npgo22/APRL-Electrical/kicadlibs/models/Texas_HTSSOP-14-1EP_4.4x5mm_P0.65mm_EP3.4x5mm_Mask3.155x3.255mm.step

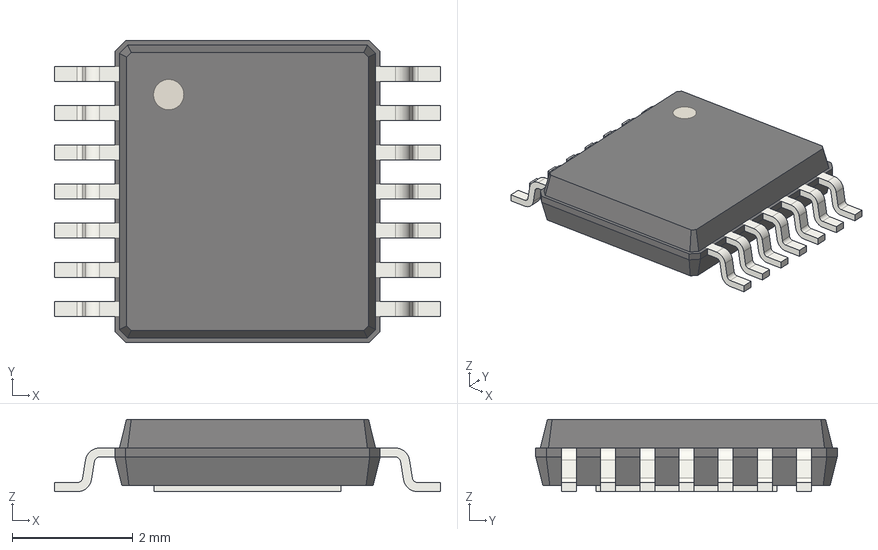
[picture p17: CAD file, 2026-09-21]
kicadlibs/models/Texas_HTSSOP-14-1EP_4.4x5mm_P0.65mm_EP3.4x5mm_Mask3.155x3.255mm.step
6.40 x 5.00 x 1.20 mm
