npgo22/APRL-Electrical/kicadlibs/models/WSON-6-1EP_2x2mm_P0.65mm_EP1x1.6mm.step

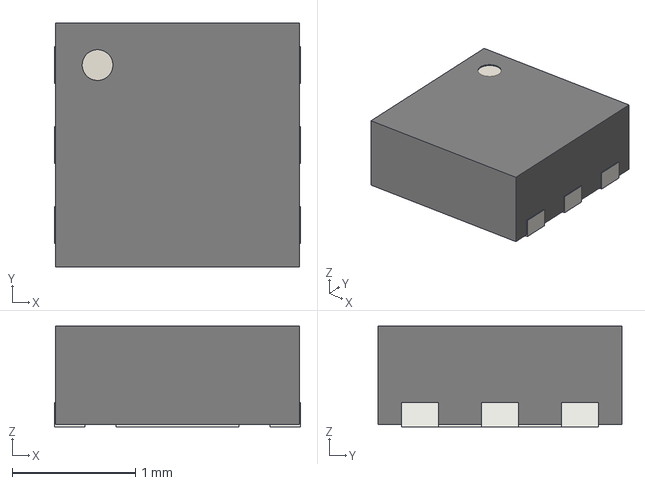
[picture p18: CAD file, 2026-09-21]
kicadlibs/models/WSON-6-1EP_2x2mm_P0.65mm_EP1x1.6mm.step
2.00 x 1.98 x 0.82 mm
