npgo22/APRL-Electrical/kicadlibs/models/Molex_CLIK-Mate_503175-0500_1x05-1MP_P1.50mm_Horizontal.step

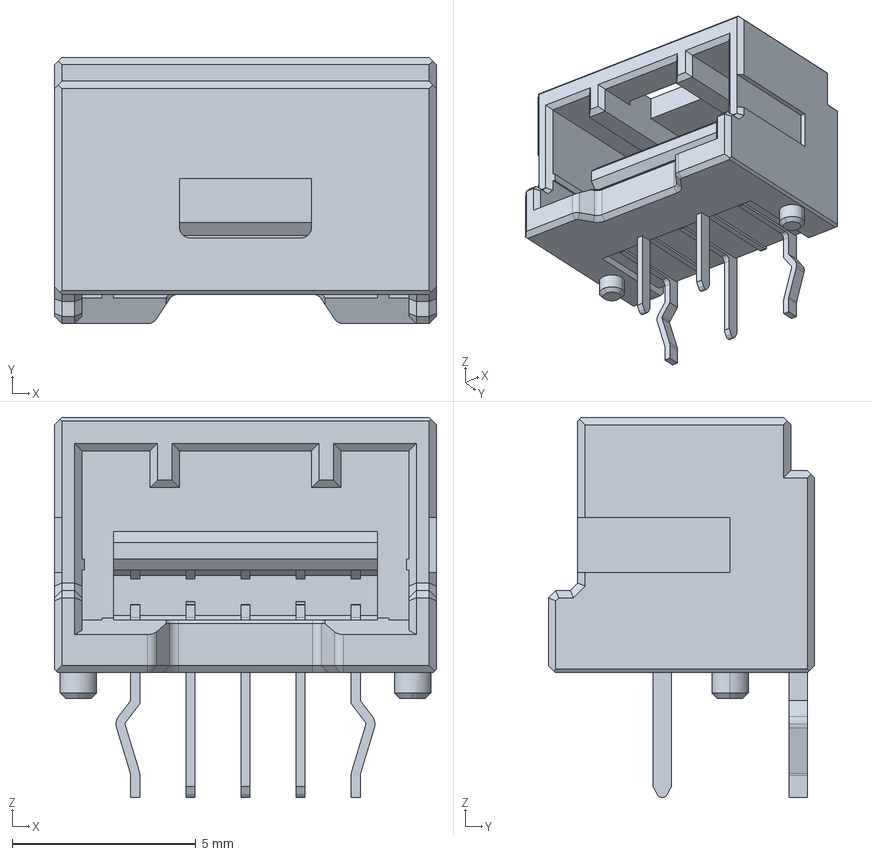
[picture p19: CAD file, 2026-09-17]
kicadlibs/models/Molex_CLIK-Mate_503175-0500_1x05-1MP_P1.50mm_Horizontal.step
10.4 x 7.25 x 10.4 mm
