npgo22/APRL-Electrical/kicadlibs/models/GPSM-SMD_NEO-M8N.step

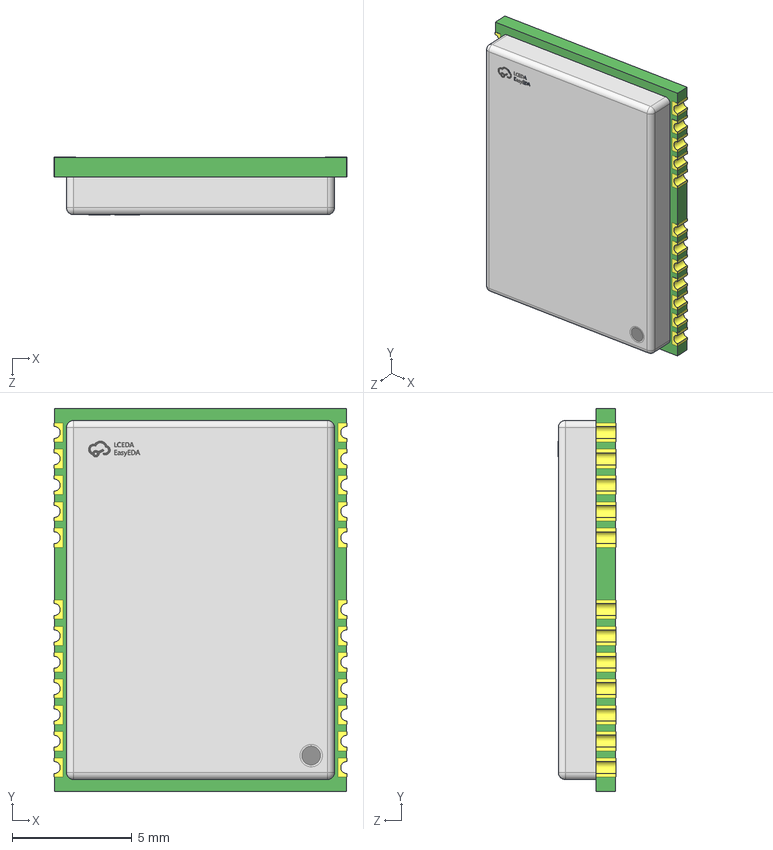
[picture p20: CAD file, 2026-09-17]
kicadlibs/models/GPSM-SMD_NEO-M8N.step
12.2 x 16.0 x 2.42 mm
