npgo22/APRL-Electrical/kicadlibs/models/Molex_CLIK-Mate_503159-1401_1x14-1MP_P1.50mm_Vertical.step

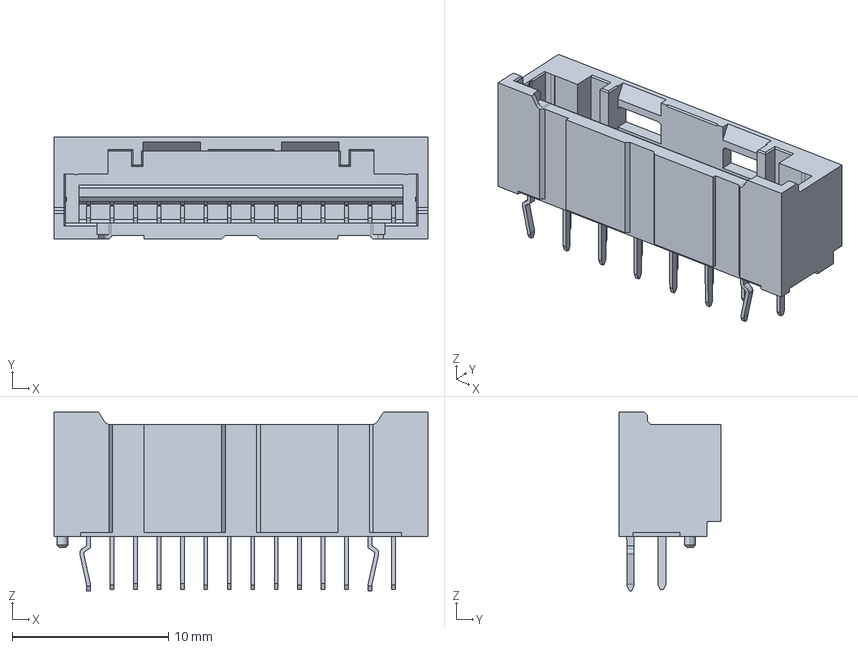
[picture p22: CAD file, 2026-09-17]
kicadlibs/models/Molex_CLIK-Mate_503159-1401_1x14-1MP_P1.50mm_Vertical.step
23.9 x 6.55 x 11.4 mm
