npgo22/APRL-Electrical/kicadlibs/models/QFN-32-1EP_5x5mm_P0.5mm_EP3.3x3.3mm.step

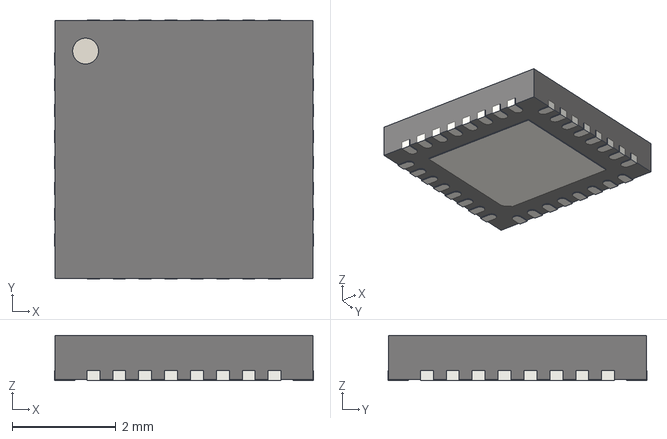
[picture p23: CAD file, 2026-09-17]
kicadlibs/models/QFN-32-1EP_5x5mm_P0.5mm_EP3.3x3.3mm.step
5.00 x 5.00 x 0.875 mm
