npgo22/APRL-Electrical/kicadlibs/models/D_SMF.step

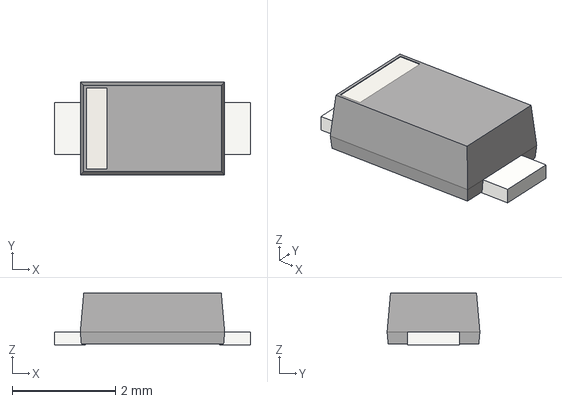
[picture p24: CAD file, 2026-09-17]
kicadlibs/models/D_SMF.step
3.80 x 1.80 x 1.00 mm
