npgo22/APRL-Electrical/kicadlibs/models/Molex_CLIK-Mate_503175-1400_1x14-1MP_P1.50mm_Horizontal.step

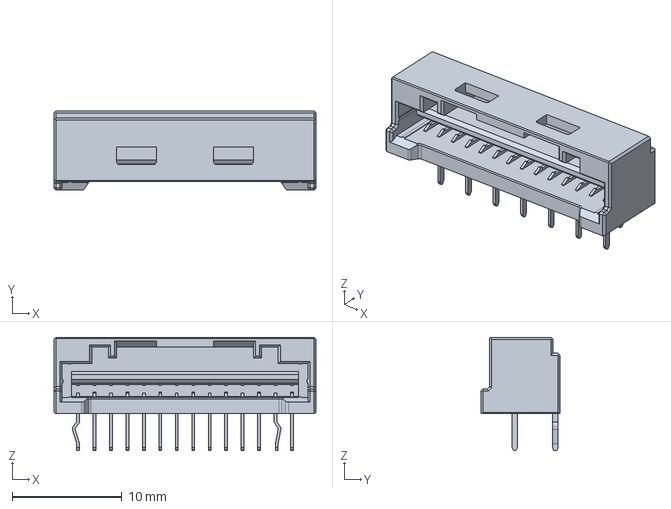
[picture p25: CAD file, 2026-09-17]
kicadlibs/models/Molex_CLIK-Mate_503175-1400_1x14-1MP_P1.50mm_Horizontal.step
23.9 x 7.25 x 10.4 mm
