npgo22/APRL-Electrical/kicadlibs/models/CRYSTAL-SMD_4P-L3.2-W2.5-BL-2.step

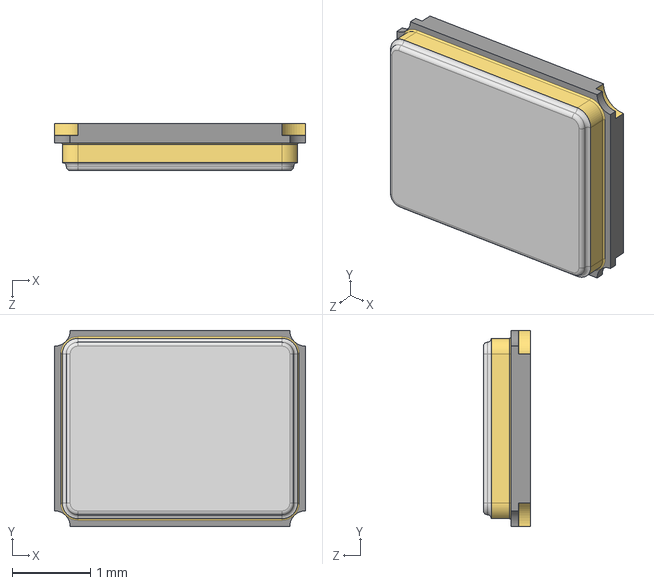
[picture p26: CAD file, 2026-09-17]
kicadlibs/models/CRYSTAL-SMD_4P-L3.2-W2.5-BL-2.step
3.20 x 2.50 x 0.601 mm
