npgo22/APRL-Electrical/kicadlibs/models/Molex_CLIK-Mate_503175-0200_1x02-1MP_P1.50mm_Horizontal.step

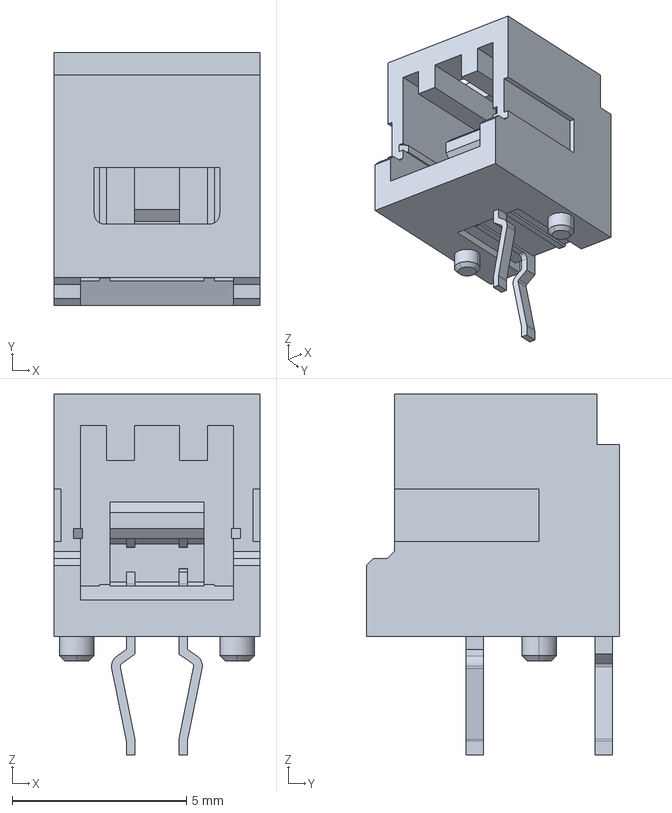
[picture p27: CAD file, 2026-09-17]
kicadlibs/models/Molex_CLIK-Mate_503175-0200_1x02-1MP_P1.50mm_Horizontal.step
5.90 x 7.25 x 10.4 mm
