npgo22/APRL-Electrical/kicadlibs/models/LQFP-48_7x7mm_P0.5mm.step

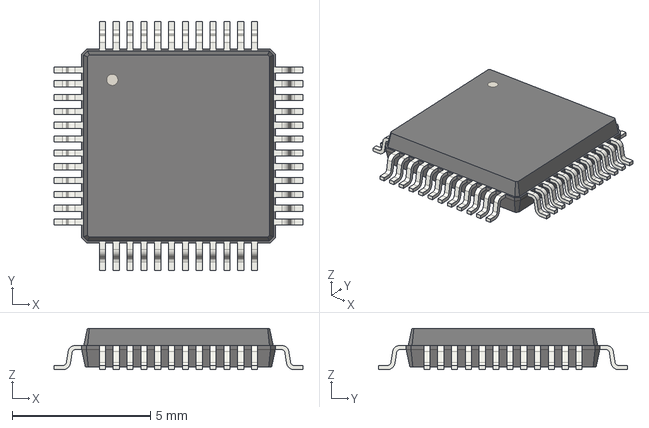
[picture p29: CAD file, 2026-09-17]
kicadlibs/models/LQFP-48_7x7mm_P0.5mm.step
9.00 x 9.00 x 1.50 mm
