npgo22/APRL-Electrical/kicadlibs/models/Molex_CLIK-Mate_503175-1300_1x13-1MP_P1.50mm_Horizontal.step

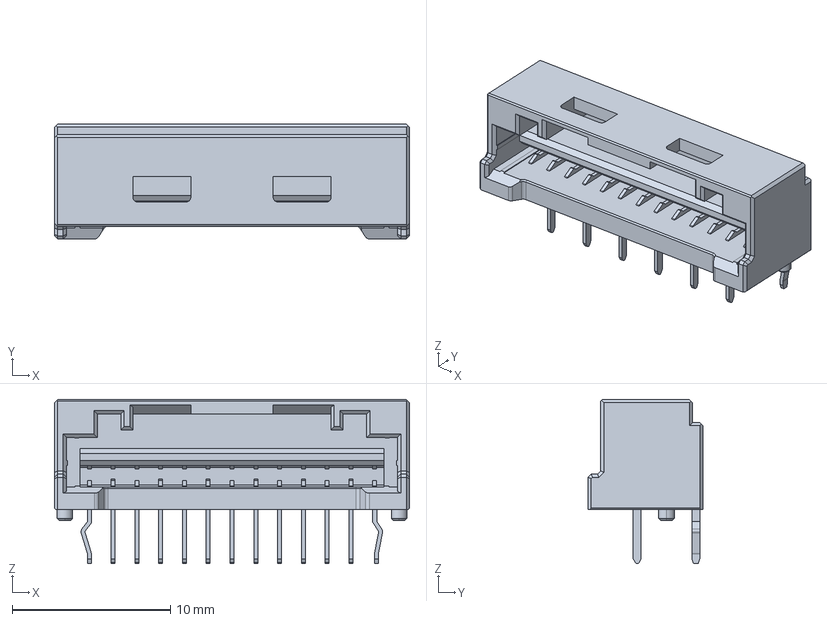
[picture p30: CAD file, 2026-09-17]
kicadlibs/models/Molex_CLIK-Mate_503175-1300_1x13-1MP_P1.50mm_Horizontal.step
22.4 x 7.25 x 10.4 mm
