npgo22/APRL-Electrical/kicadlibs/models/Molex_CLIK-Mate_503175-0300_1x03-1MP_P1.50mm_Horizontal.step

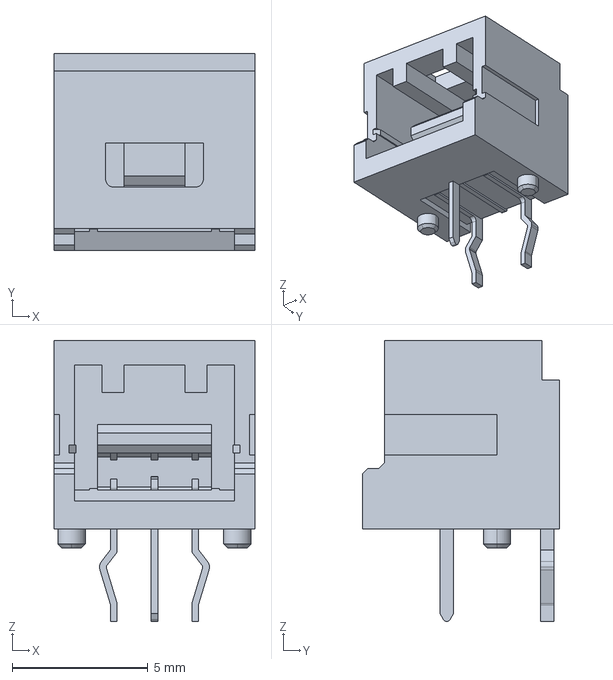
[picture p31: CAD file, 2026-09-17]
kicadlibs/models/Molex_CLIK-Mate_503175-0300_1x03-1MP_P1.50mm_Horizontal.step
7.40 x 7.25 x 10.4 mm
