npgo22/APRL-Electrical/kicadlibs/models/Molex_CLIK-Mate_503175-0800_1x08-1MP_P1.50mm_Horizontal.step

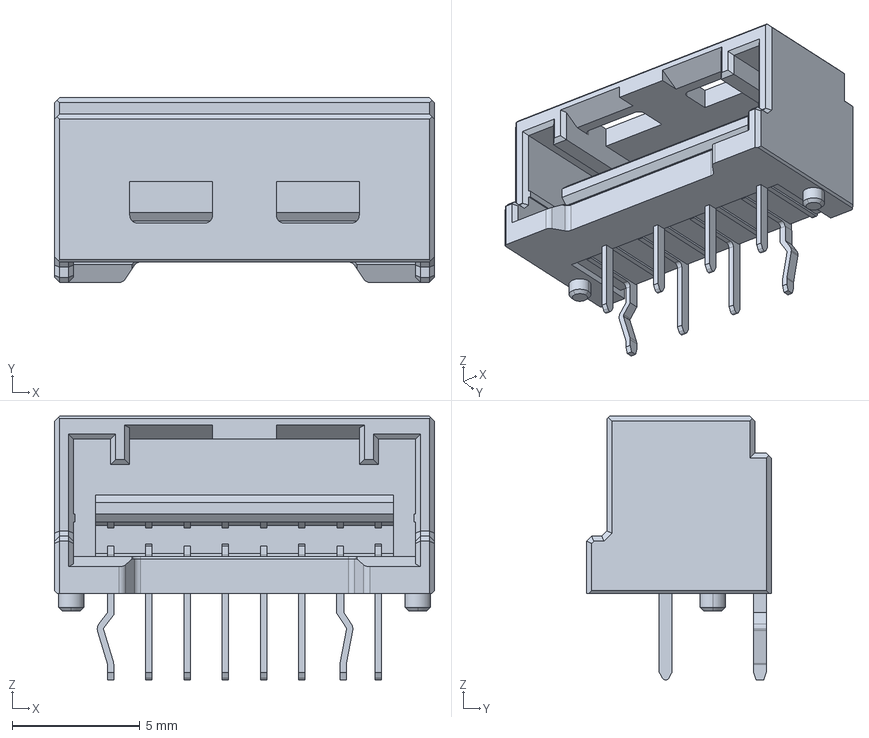
[picture p32: CAD file, 2026-09-17]
kicadlibs/models/Molex_CLIK-Mate_503175-0800_1x08-1MP_P1.50mm_Horizontal.step
14.9 x 7.25 x 10.4 mm
