npgo22/APRL-Electrical/kicadlibs/models/PhoenixContact_MSTB_2,5_2-GF-5,08_1x02_P5.08mm_Horizontal_ThreadedFlange_MountHole.step

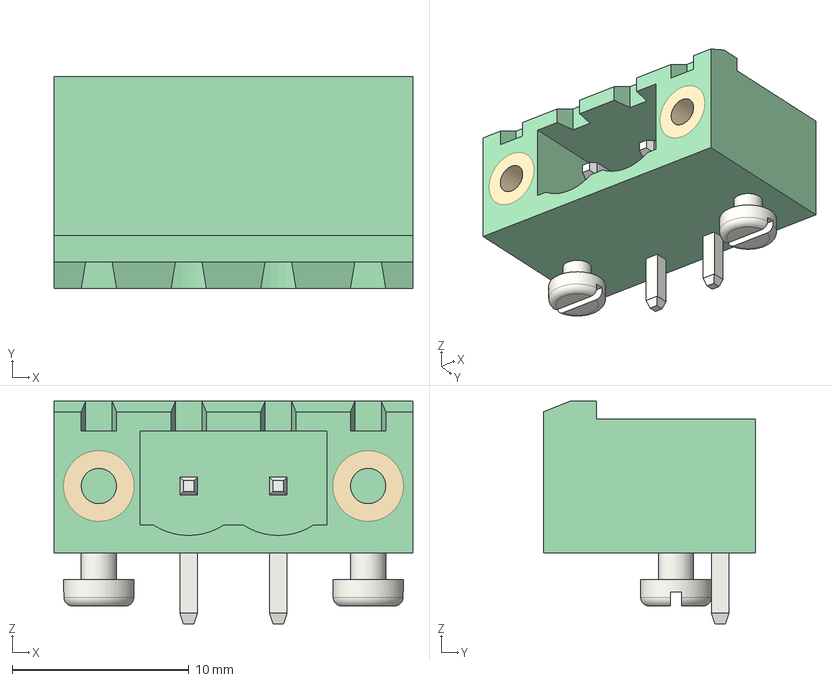
[picture p33: CAD file, 2026-09-17]
kicadlibs/models/PhoenixContact_MSTB_2,5_2-GF-5,08_1x02_P5.08mm_Horizontal_ThreadedFlange_MountHole.step
20.3 x 12.0 x 12.6 mm
