npgo22/APRL-Electrical/kicadlibs/models/R_0805_2012Metric.step

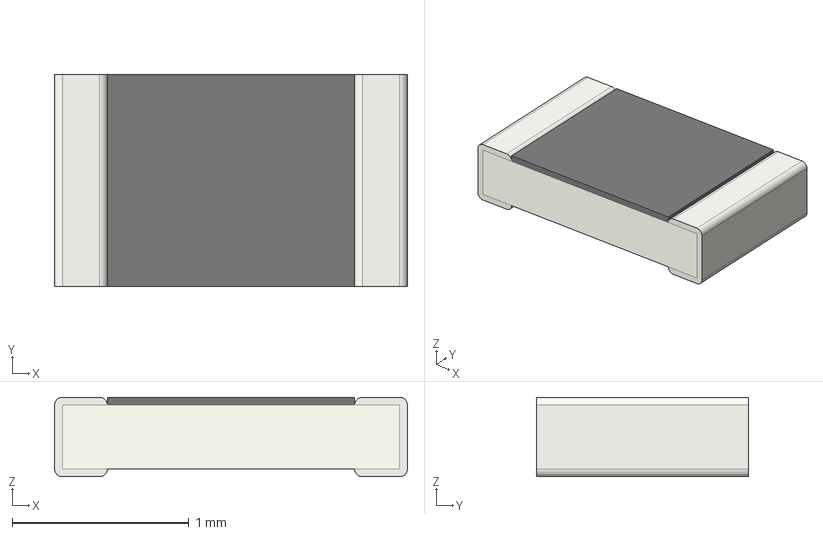
[picture p34: CAD file, 2026-09-17]
kicadlibs/models/R_0805_2012Metric.step
2.00 x 1.20 x 0.45 mm
