npgo22/APRL-Electrical/kicadlibs/models/TerminalBlock_Phoenix_MKDS-1,5-2-5.08_1x02_P5.08mm_Horizontal.step

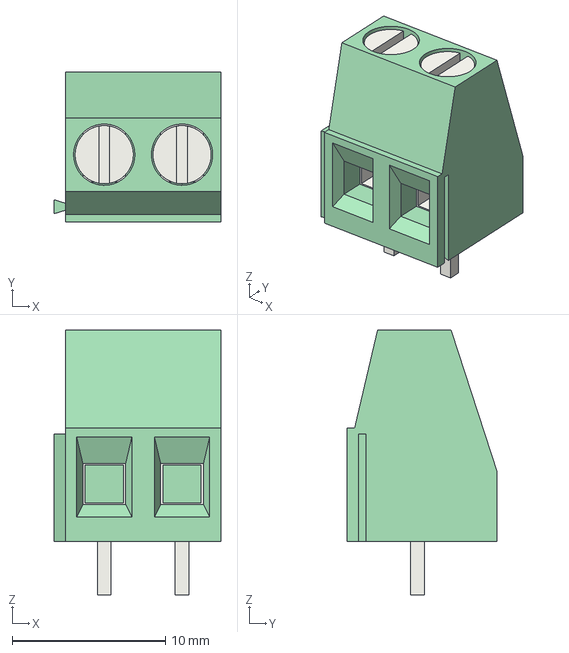
[picture p36: CAD file, 2026-09-17]
kicadlibs/models/TerminalBlock_Phoenix_MKDS-1,5-2-5.08_1x02_P5.08mm_Horizontal.step
10.9 x 9.80 x 17.3 mm
