npgo22/APRL-Electrical/kicadlibs/models/Molex_CLIK-Mate_503175-1100_1x11-1MP_P1.50mm_Horizontal.step

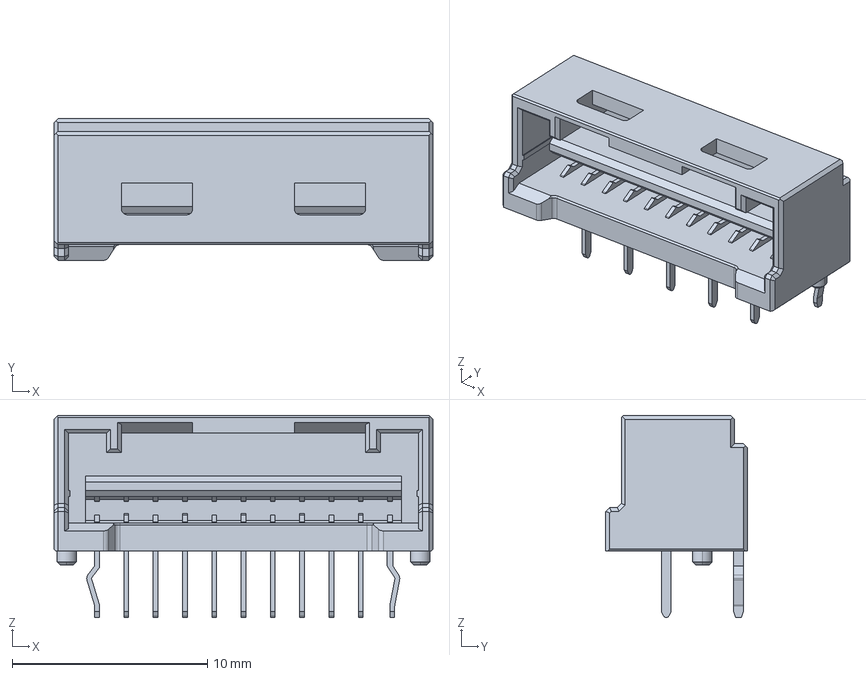
[picture p37: CAD file, 2026-09-17]
kicadlibs/models/Molex_CLIK-Mate_503175-1100_1x11-1MP_P1.50mm_Horizontal.step
19.4 x 7.25 x 10.4 mm
