npgo22/APRL-Electrical/kicadlibs/models/IDC-Header_2x09_P2.54mm_Vertical.step

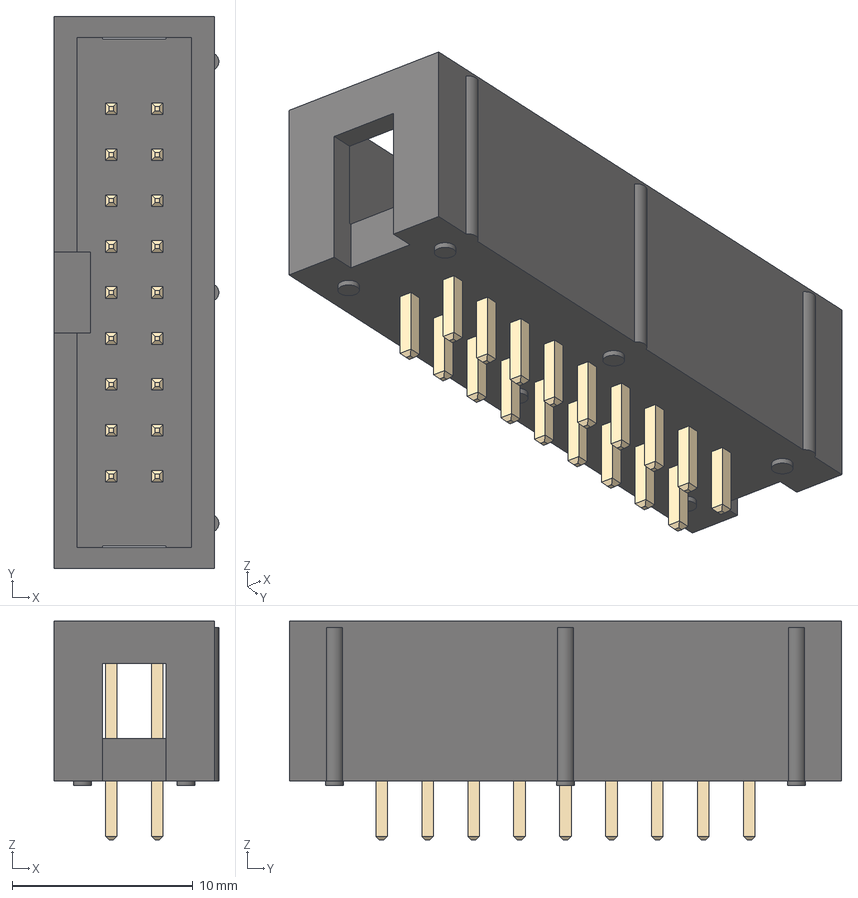
[picture p38: CAD file, 2026-09-17]
kicadlibs/models/IDC-Header_2x09_P2.54mm_Vertical.step
9.10 x 30.5 x 12.1 mm
