npgo22/APRL-Electrical/kicadlibs/models/RJ45-TH_HR911105A.step

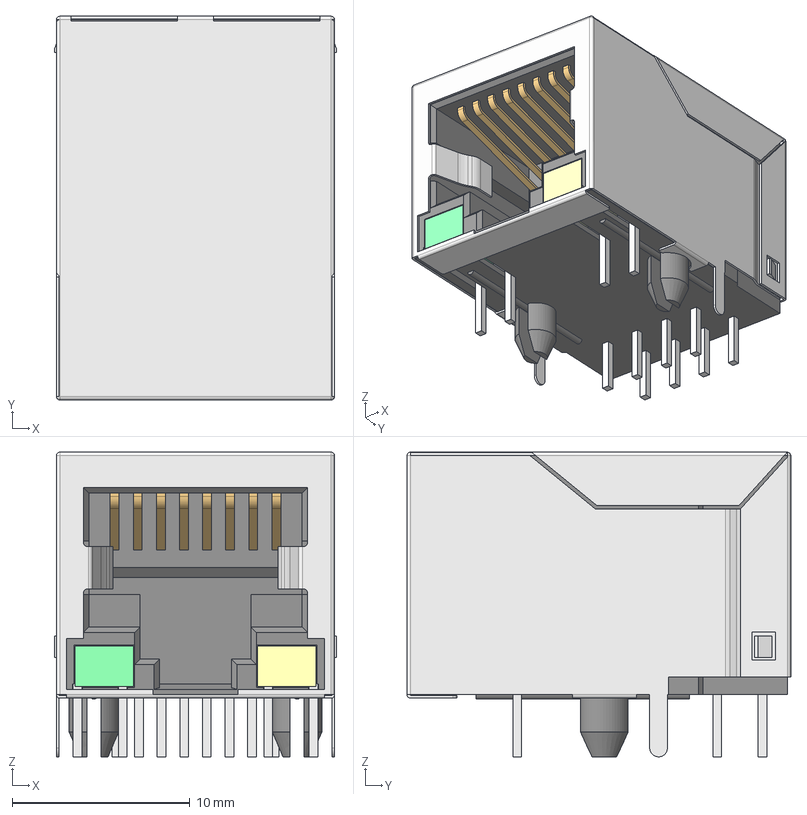
[picture p39: CAD file, 2026-09-17]
kicadlibs/models/RJ45-TH_HR911105A.step
15.9 x 21.6 x 17.1 mm
