npgo22/APRL-Electrical/kicadlibs/models/SOP-12_L5.6-W4.4-P0.80-LS7.0-BL.step

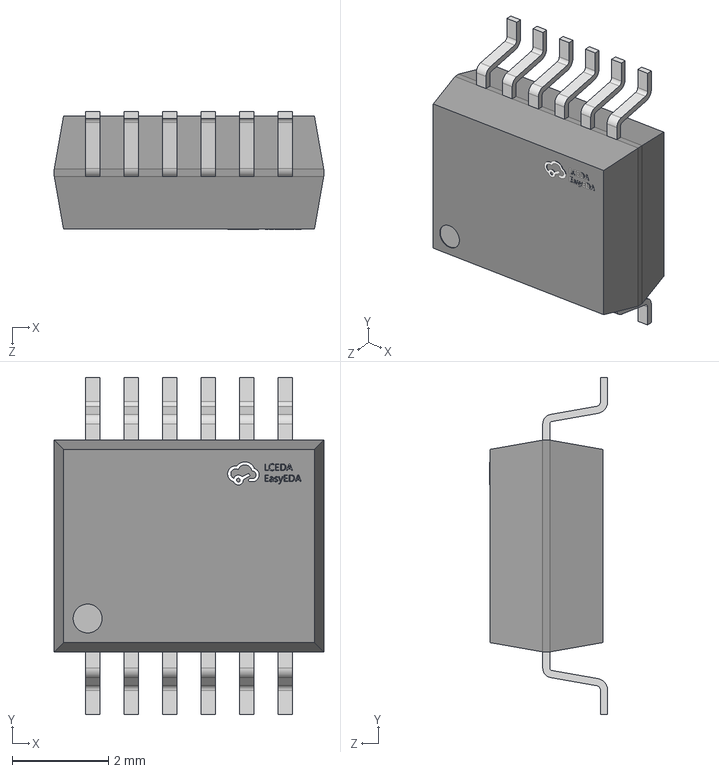
[picture p40: CAD file, 2026-09-17]
kicadlibs/models/SOP-12_L5.6-W4.4-P0.80-LS7.0-BL.step
5.60 x 7.00 x 2.46 mm
