npgo22/APRL-Electrical/kicadlibs/models/Fuse_0805_2012Metric.step

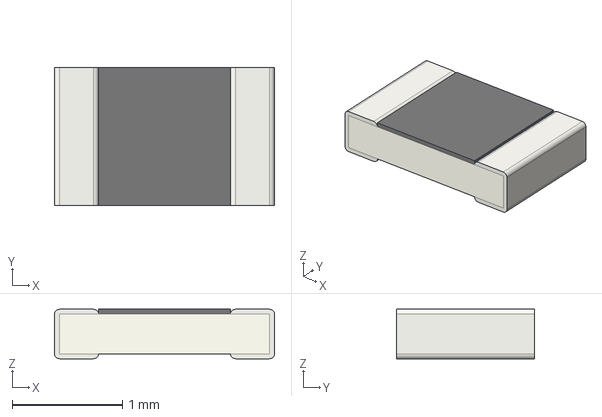
[picture p41: CAD file, 2026-09-17]
kicadlibs/models/Fuse_0805_2012Metric.step
2.00 x 1.25 x 0.45 mm
