npgo22/APRL-Electrical/kicadlibs/models/WSON-6_1.5x1.5mm_P0.5mm.step

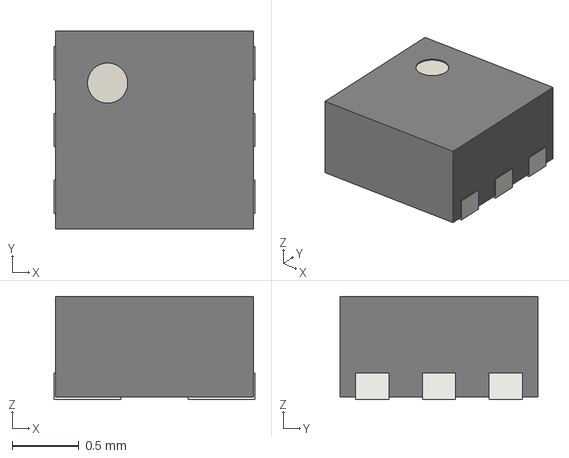
[picture p42: CAD file, 2026-09-17]
kicadlibs/models/WSON-6_1.5x1.5mm_P0.5mm.step
1.50 x 1.48 x 0.77 mm
