npgo22/APRL-Electrical/kicadlibs/models/DFN-8-1EP_3x3mm_P0.65mm_EP1.55x2.4mm.step

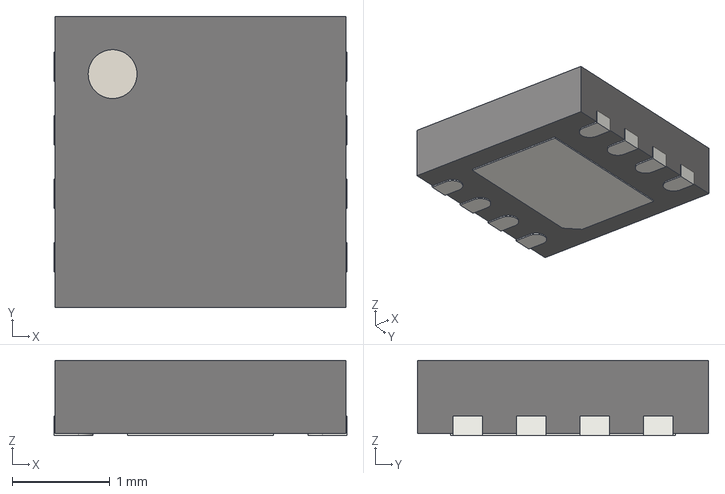
[picture p43: CAD file, 2026-09-17]
kicadlibs/models/DFN-8-1EP_3x3mm_P0.65mm_EP1.55x2.4mm.step
3.00 x 2.98 x 0.77 mm
