npgo22/APRL-Electrical/kicadlibs/models/Molex_CLIK-Mate_503159-1501_1x15-1MP_P1.50mm_Vertical.step

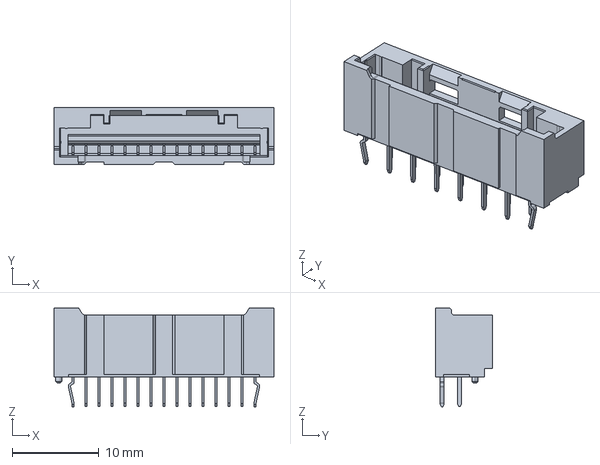
[picture p44: CAD file, 2026-09-17]
kicadlibs/models/Molex_CLIK-Mate_503159-1501_1x15-1MP_P1.50mm_Vertical.step
25.4 x 6.55 x 11.4 mm
