npgo22/APRL-Electrical/kicadlibs/models/QFN-32-1EP_5x5mm_P0.5mm_EP3.45x3.45mm.step

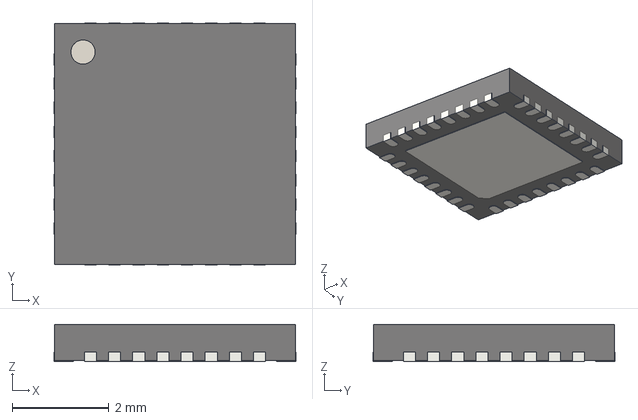
[picture p46: CAD file, 2026-09-17]
kicadlibs/models/QFN-32-1EP_5x5mm_P0.5mm_EP3.45x3.45mm.step
5.00 x 5.00 x 0.77 mm
