npgo22/APRL-Electrical/kicadlibs/models/s02-25200300.step

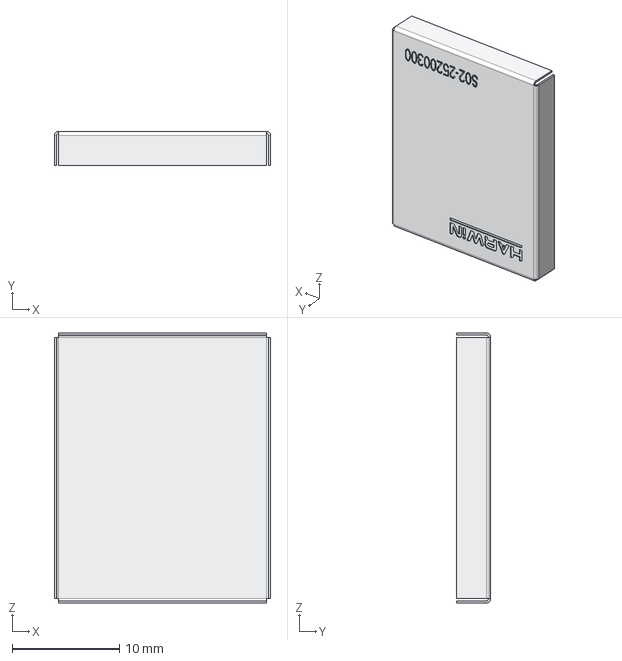
[picture p47: CAD file, 2026-09-17]
kicadlibs/models/s02-25200300.step
20.2 x 3.20 x 25.2 mm
