npgo22/APRL-Electrical/kicadlibs/models/DFN8_2x3MC_MCH.step

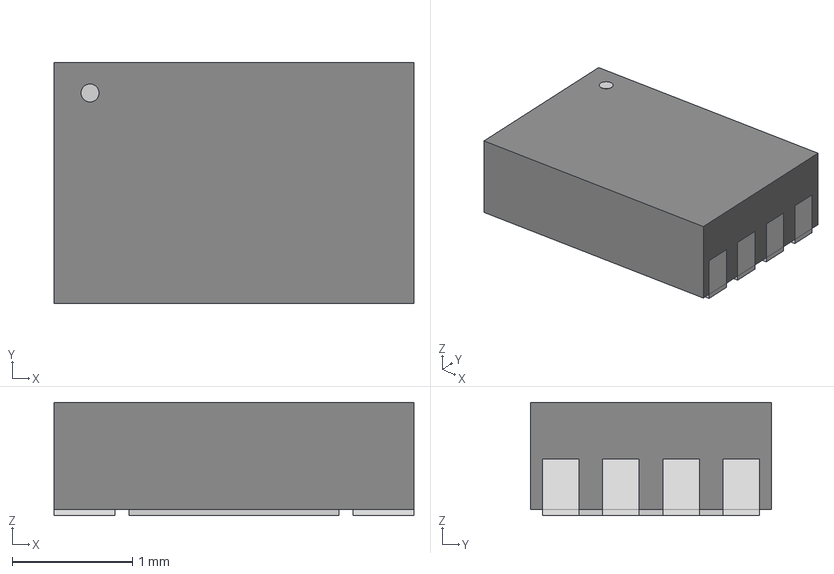
[picture p48: CAD file, 2026-09-17]
kicadlibs/models/DFN8_2x3MC_MCH.step
3.00 x 2.01 x 0.942 mm
