npgo22/APRL-Electrical/kicadlibs/models/TQFP-32.STEP

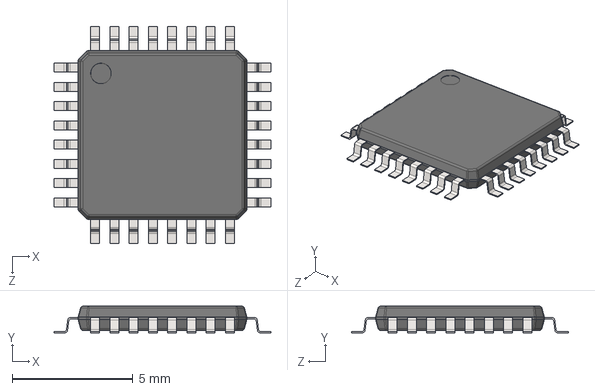
[picture p49: CAD file, 2026-09-17]
kicadlibs/models/TQFP-32.STEP
9.00 x 1.10 x 9.00 mm
