npgo22/APRL-Electrical/kicadlibs/models/PinHeader_1x05_P2.54mm_Vertical.step

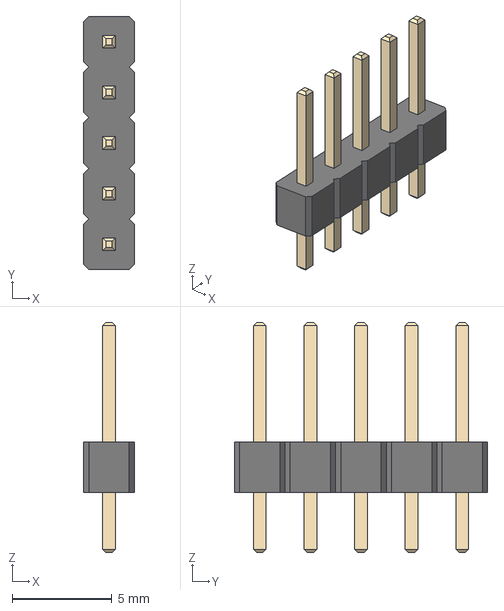
[picture p50: CAD file, 2026-09-17]
kicadlibs/models/PinHeader_1x05_P2.54mm_Vertical.step
2.54 x 12.7 x 11.5 mm
