npgo22/APRL-Electrical/kicadlibs/models/IDC-Header_2x06_P2.54mm_Vertical.step

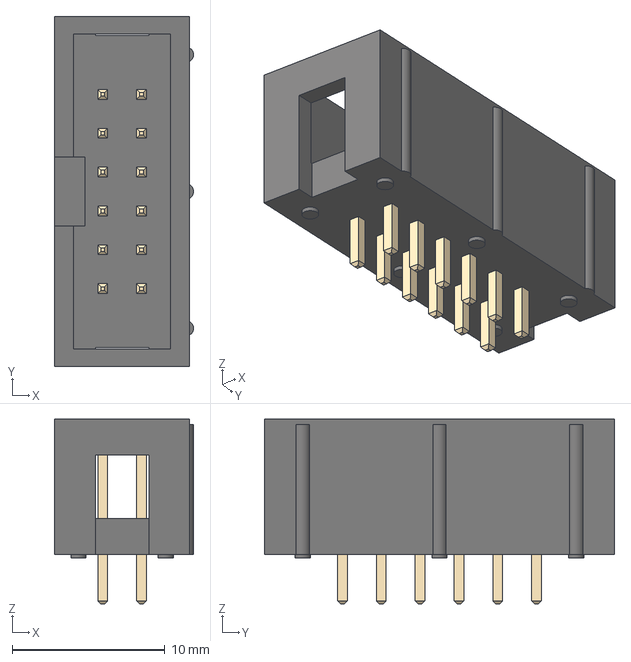
[picture p51: CAD file, 2026-09-17]
kicadlibs/models/IDC-Header_2x06_P2.54mm_Vertical.step
9.10 x 22.9 x 12.1 mm
