npgo22/APRL-Electrical/kicadlibs/models/Molex_CLIK-Mate_503175-1500_1x15-1MP_P1.50mm_Horizontal.step

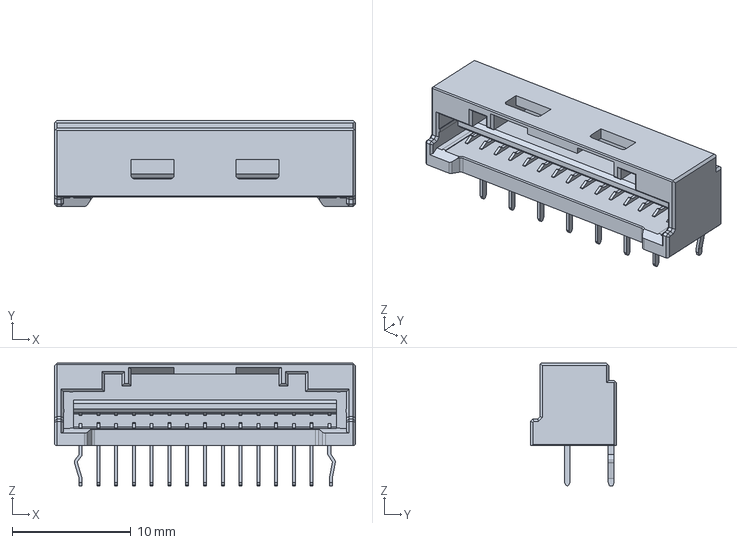
[picture p52: CAD file, 2026-09-17]
kicadlibs/models/Molex_CLIK-Mate_503175-1500_1x15-1MP_P1.50mm_Horizontal.step
25.4 x 7.25 x 10.4 mm
