npgo22/APRL-Electrical/kicadlibs/models/L_0402_1005Metric.step

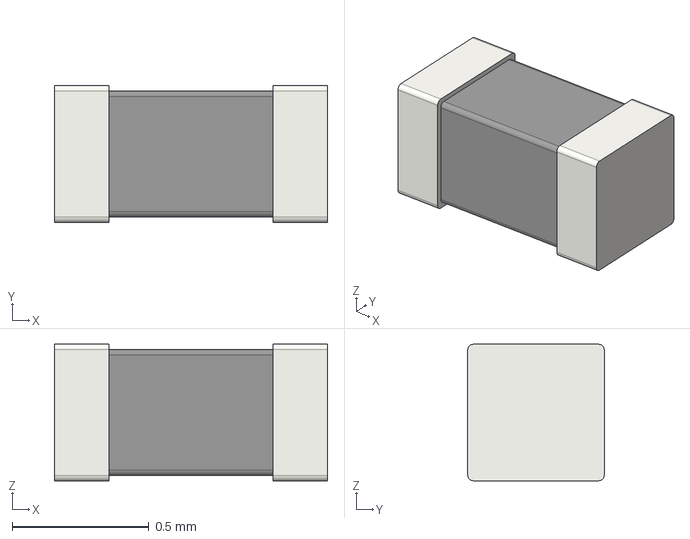
[picture p53: CAD file, 2026-09-17]
kicadlibs/models/L_0402_1005Metric.step
1.00 x 0.5 x 0.5 mm
