npgo22/APRL-Electrical/kicadlibs/models/PhoenixContact_MSTBV_2,5_2-GF-5,08_1x02_P5.08mm_Vertical_ThreadedFlange_MountHole.step

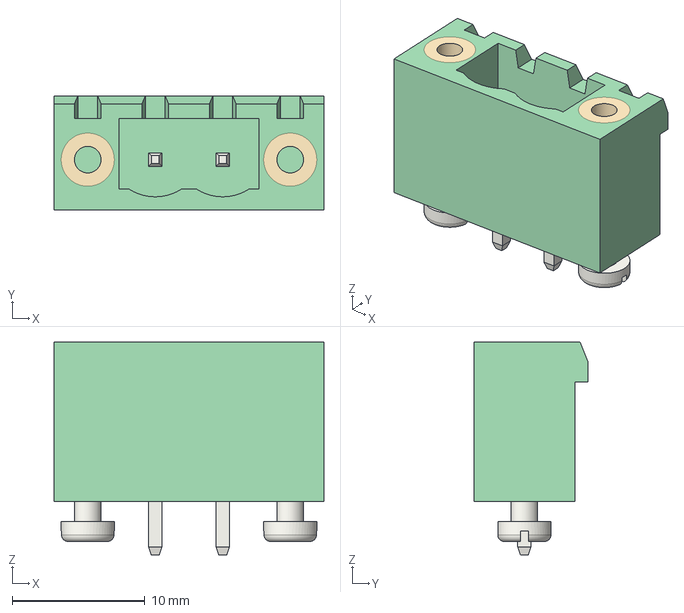
[picture p54: CAD file, 2026-09-17]
kicadlibs/models/PhoenixContact_MSTBV_2,5_2-GF-5,08_1x02_P5.08mm_Vertical_ThreadedFlange_MountHole.step
20.3 x 8.60 x 16.0 mm
