npgo22/APRL-Electrical/kicadlibs/models/SOT-23-5.step

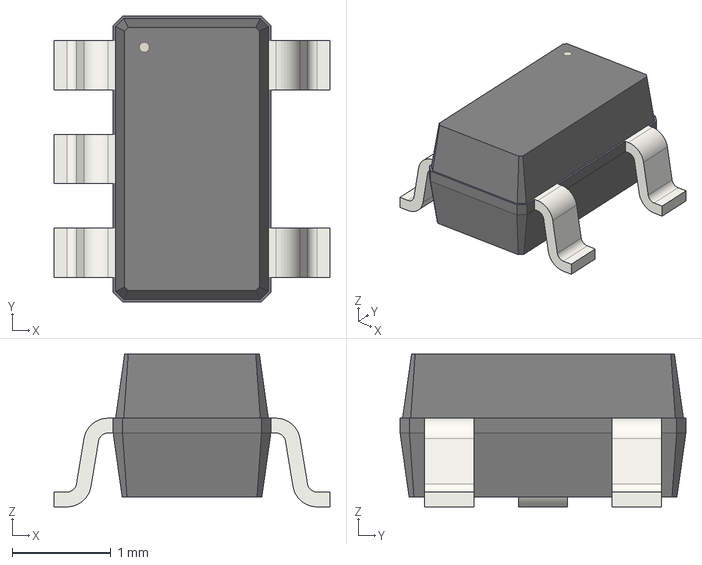
[picture p55: CAD file, 2026-09-17]
kicadlibs/models/SOT-23-5.step
2.80 x 2.90 x 1.55 mm
