npgo22/APRL-Electrical/kicadlibs/models/Molex_CLIK-Mate_503159-0401_1x04-1MP_P1.50mm_Vertical.step

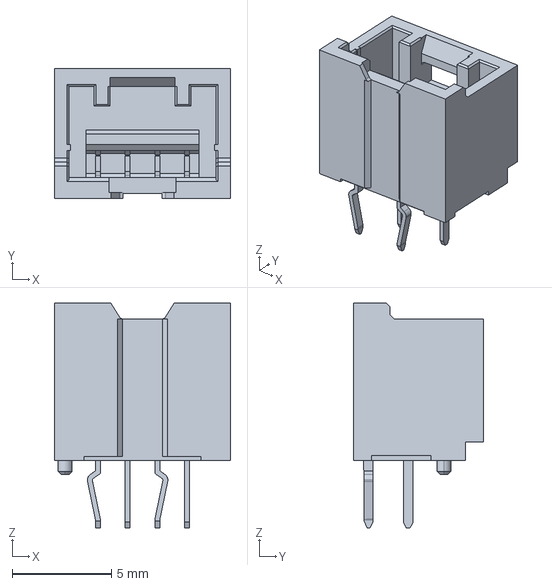
[picture p56: CAD file, 2026-09-17]
kicadlibs/models/Molex_CLIK-Mate_503159-0401_1x04-1MP_P1.50mm_Vertical.step
8.90 x 6.55 x 11.4 mm
