npgo22/APRL-Electrical/kicadlibs/models/LQFP-64_10x10mm_P0.5mm.step

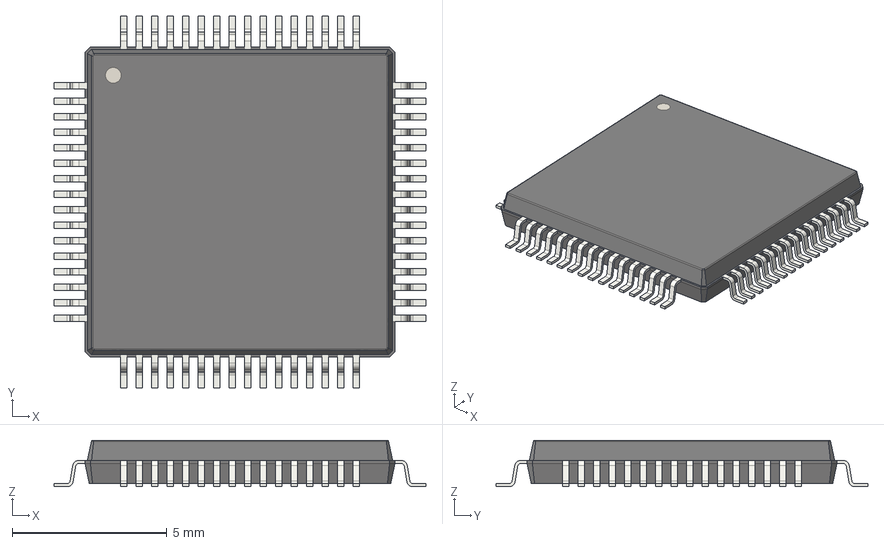
[picture p57: CAD file, 2026-09-17]
kicadlibs/models/LQFP-64_10x10mm_P0.5mm.step
12.0 x 12.0 x 1.50 mm
