npgo22/APRL-Electrical/kicadlibs/models/Molex_CLIK-Mate_503175-1200_1x12-1MP_P1.50mm_Horizontal.step

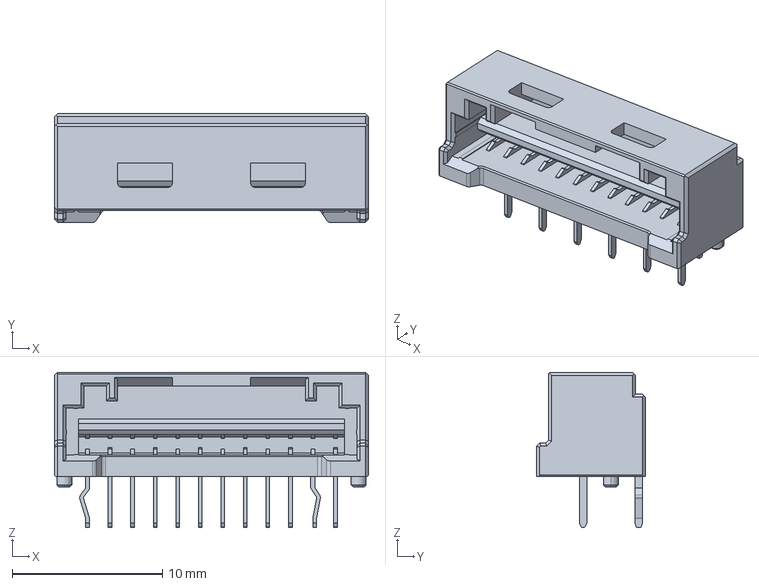
[picture p58: CAD file, 2026-09-17]
kicadlibs/models/Molex_CLIK-Mate_503175-1200_1x12-1MP_P1.50mm_Horizontal.step
20.9 x 7.25 x 10.4 mm
