npgo22/APRL-Electrical/kicadlibs/models/C_0805_2012Metric.step

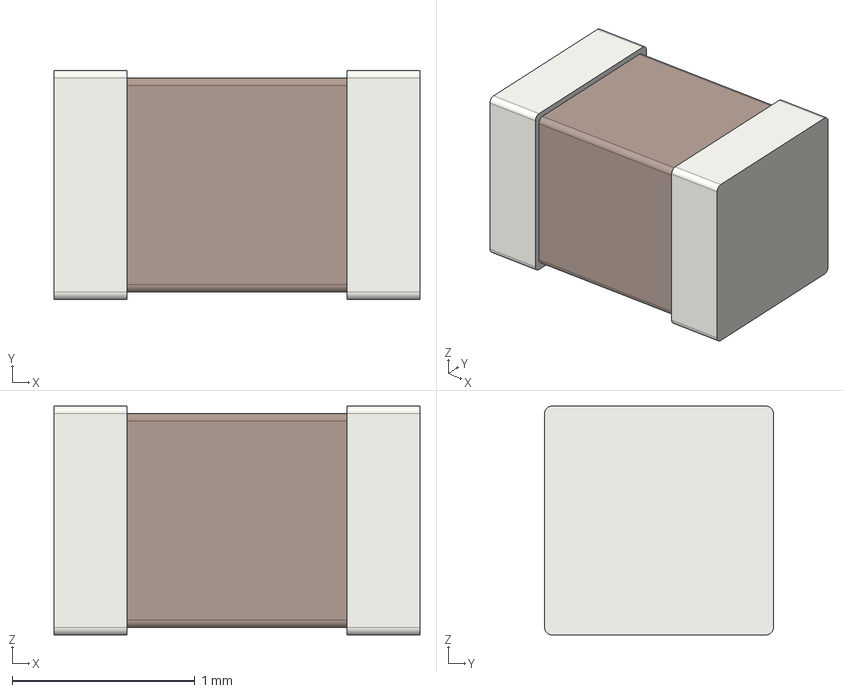
[picture p59: CAD file, 2026-09-17]
kicadlibs/models/C_0805_2012Metric.step
2.00 x 1.25 x 1.25 mm
