npgo22/APRL-Electrical/kicadlibs/models/QFN-24-1EP_4x4mm_P0.5mm_EP2.6x2.6mm.step

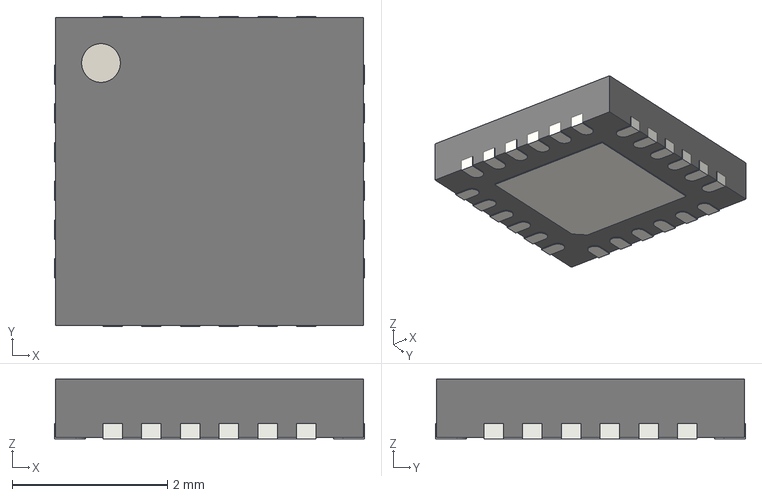
[picture p60: CAD file, 2026-09-17]
kicadlibs/models/QFN-24-1EP_4x4mm_P0.5mm_EP2.6x2.6mm.step
4.00 x 4.00 x 0.77 mm
