npgo22/APRL-Electrical/kicadlibs/models/Molex_CLIK-Mate_503175-1000_1x10-1MP_P1.50mm_Horizontal.step

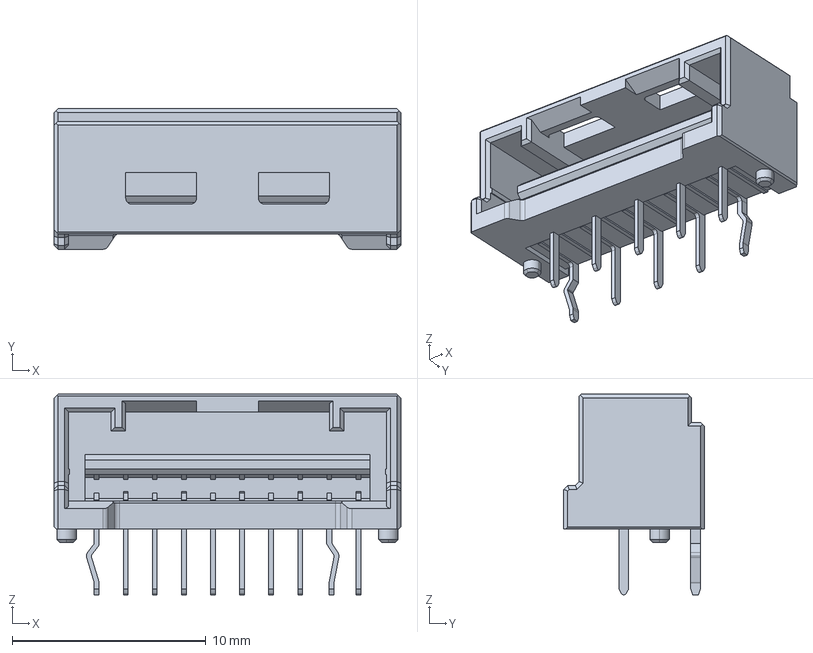
[picture p61: CAD file, 2026-09-17]
kicadlibs/models/Molex_CLIK-Mate_503175-1000_1x10-1MP_P1.50mm_Horizontal.step
17.9 x 7.25 x 10.4 mm
