npgo22/APRL-Electrical/kicadlibs/models/Molex_CLIK-Mate_503175-0700_1x07-1MP_P1.50mm_Horizontal.step

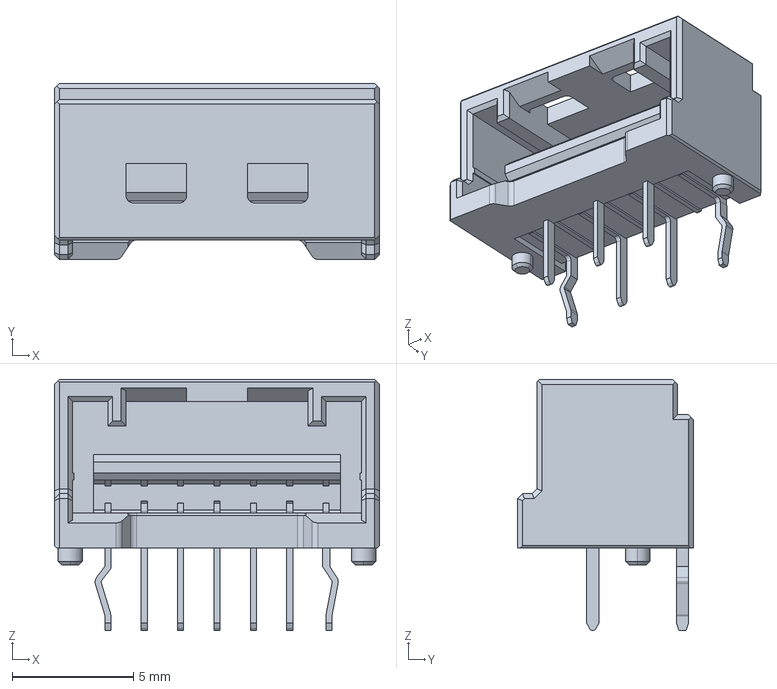
[picture p62: CAD file, 2026-09-17]
kicadlibs/models/Molex_CLIK-Mate_503175-0700_1x07-1MP_P1.50mm_Horizontal.step
13.4 x 7.25 x 10.4 mm
