npgo22/APRL-Electrical/kicadlibs/models/TerminalBlock_Phoenix_MPT-0,5-8-2.54_1x08_P2.54mm_Horizontal.step

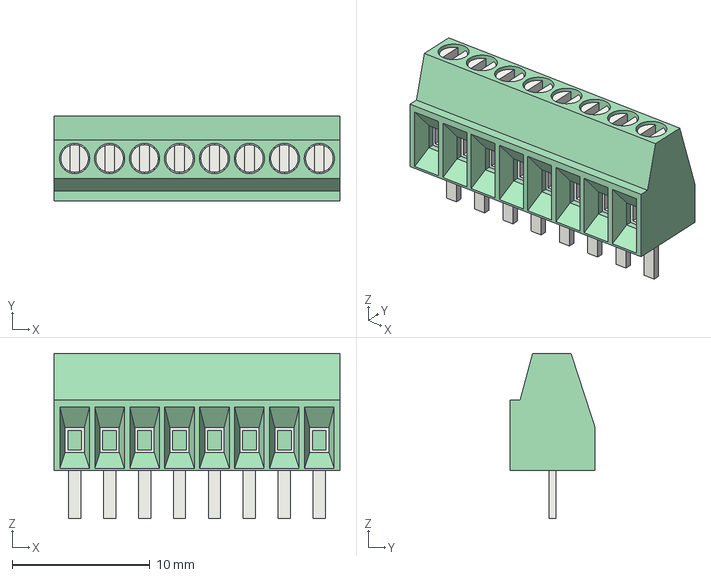
[picture p63: CAD file, 2026-09-17]
kicadlibs/models/TerminalBlock_Phoenix_MPT-0,5-8-2.54_1x08_P2.54mm_Horizontal.step
20.8 x 6.20 x 12.0 mm
