npgo22/APRL-Electrical/kicadlibs/models/BatteryHolder_Keystone_1042_1x18650.step

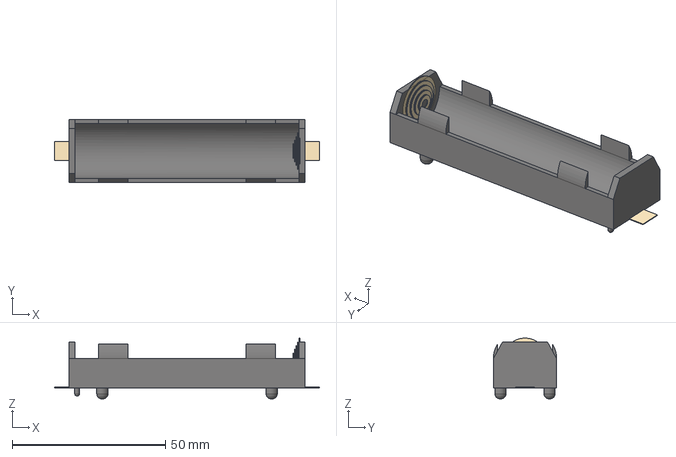
[picture p64: CAD file, 2026-09-17]
kicadlibs/models/BatteryHolder_Keystone_1042_1x18650.step
86.4 x 20.6 x 19.8 mm
