npgo22/APRL-Electrical/kicadlibs/models/SOIC-8_3.9x4.9mm_P1.27mm.step

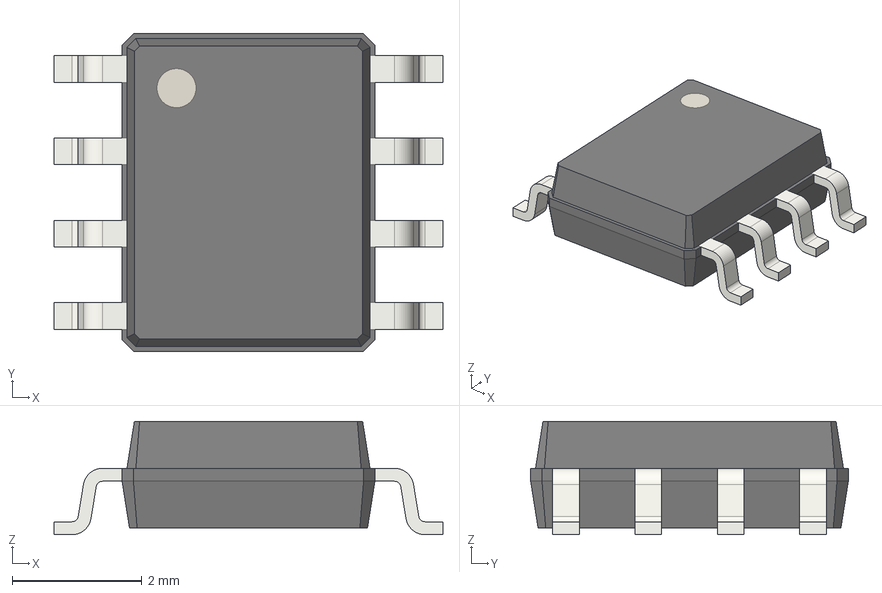
[picture p65: CAD file, 2026-09-17]
kicadlibs/models/SOIC-8_3.9x4.9mm_P1.27mm.step
6.00 x 4.90 x 1.75 mm
