npgo22/APRL-Electrical/kicadlibs/models/Molex_CLIK-Mate_503159-0201_1x02-1MP_P1.50mm_Vertical.step

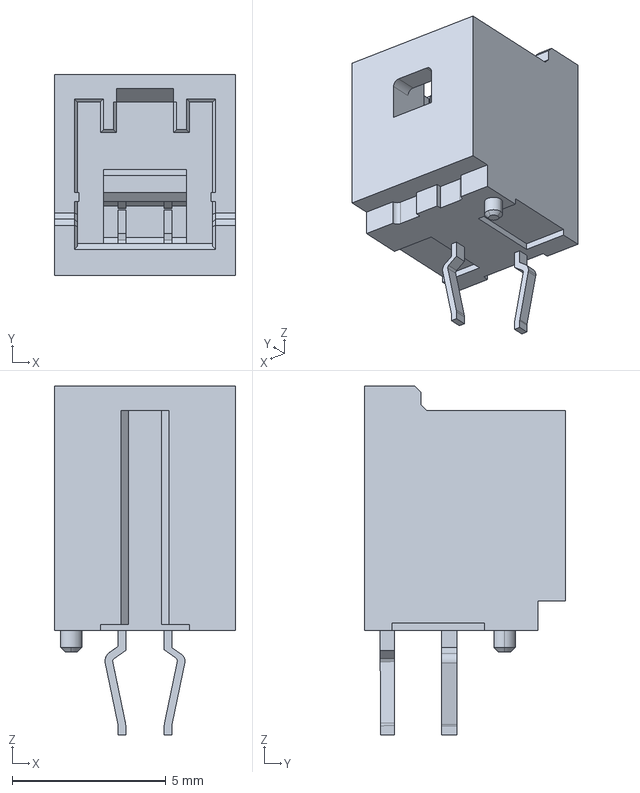
[picture p66: CAD file, 2026-09-17]
kicadlibs/models/Molex_CLIK-Mate_503159-0201_1x02-1MP_P1.50mm_Vertical.step
5.90 x 6.55 x 11.4 mm
