npgo22/APRL-Electrical/kicadlibs/models/PinHeader_2x01_P2.54mm_Vertical.step

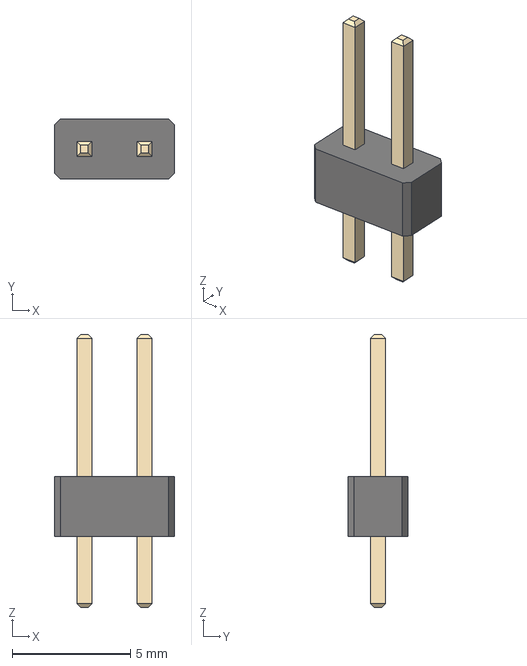
[picture p68: CAD file, 2026-09-17]
kicadlibs/models/PinHeader_2x01_P2.54mm_Vertical.step
5.08 x 2.54 x 11.5 mm
