npgo22/APRL-Electrical/kicadlibs/models/D_SOD-323.step

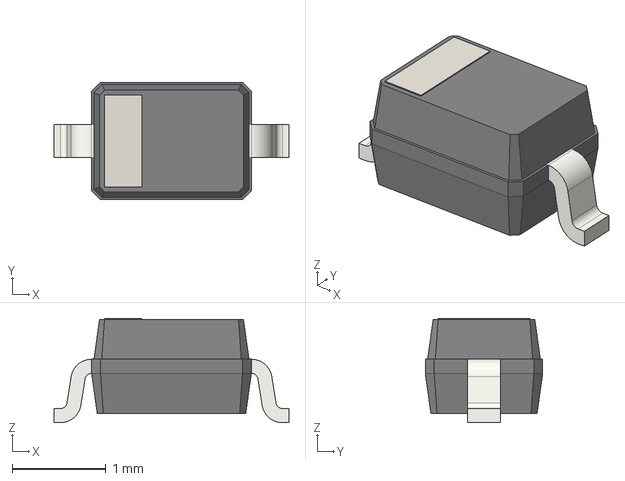
[picture p69: CAD file, 2026-09-17]
kicadlibs/models/D_SOD-323.step
2.50 x 1.25 x 1.11 mm
