npgo22/APRL-Electrical/kicadlibs/models/VQFN-24_L4.0-W4.0-P0.50-BL-EP2.5.step

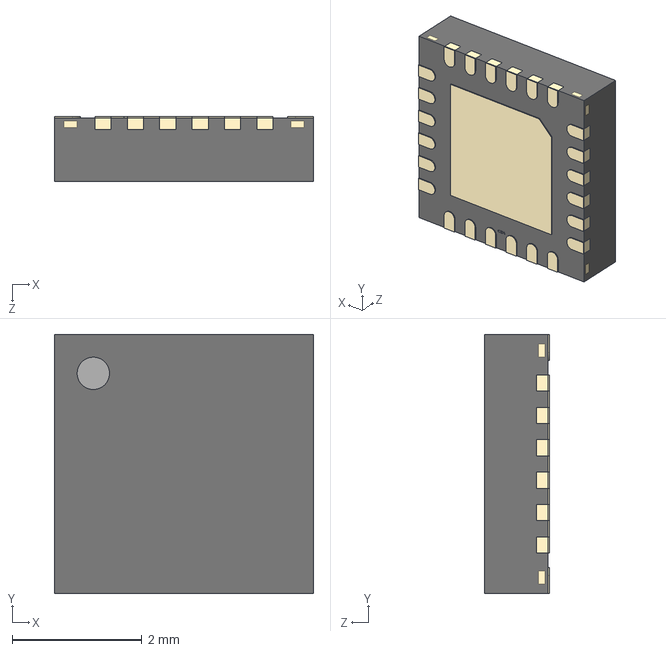
[picture p72: CAD file, 2026-09-17]
kicadlibs/models/VQFN-24_L4.0-W4.0-P0.50-BL-EP2.5.step
4.00 x 4.00 x 1.00 mm
