npgo22/APRL-Electrical/kicadlibs/models/USB-C_SMD-TYPE-C-31-M-12_1.step

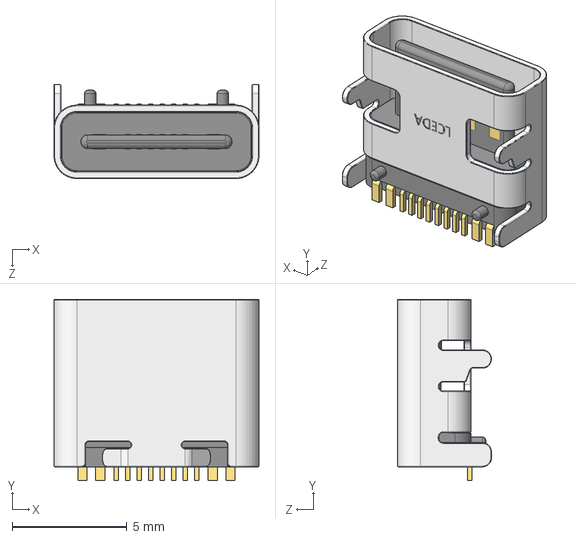
[picture p73: CAD file, 2026-09-17]
kicadlibs/models/USB-C_SMD-TYPE-C-31-M-12_1.step
8.94 x 7.90 x 4.10 mm
