npgo22/APRL-Electrical/kicadlibs/models/HRO_TYPE-C-31-M-12.step

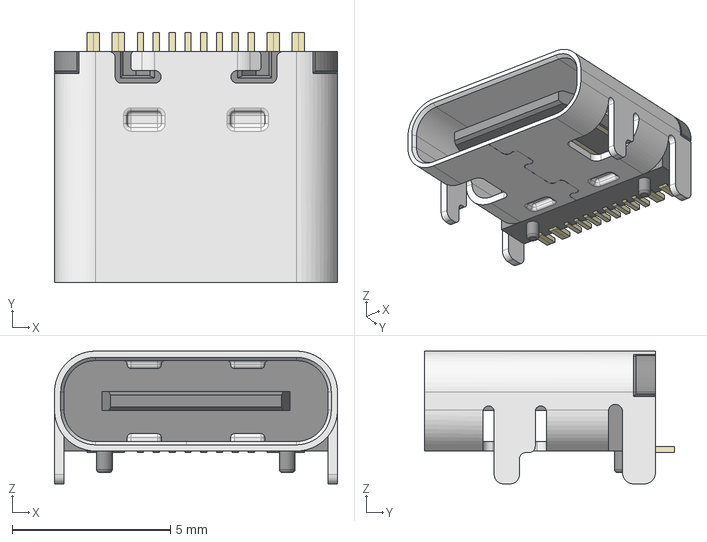
[picture p74: CAD file, 2026-09-17]
kicadlibs/models/HRO_TYPE-C-31-M-12.step
8.95 x 7.90 x 4.20 mm
