npgo22/APRL-Electrical/kicadlibs/models/Ublox_LEA_M8T.step

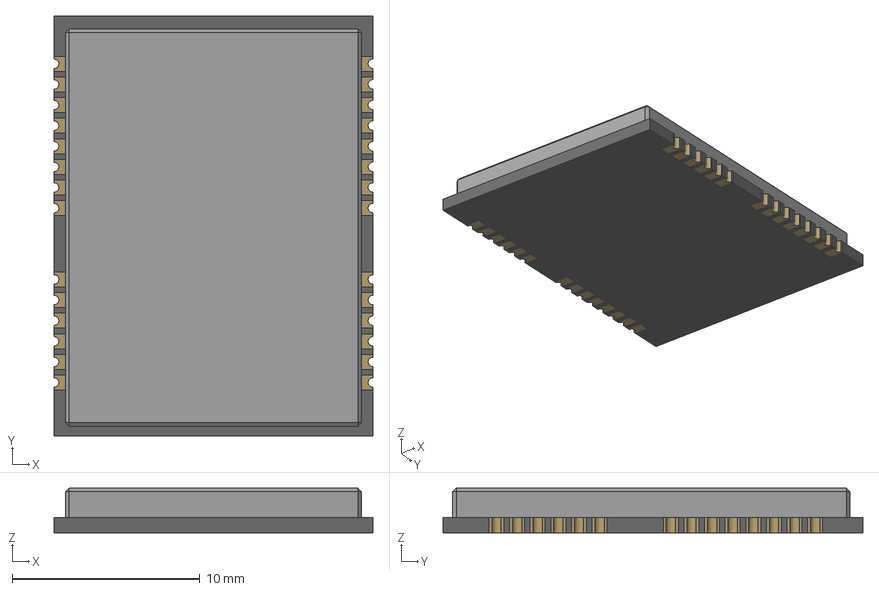
[picture p75: CAD file, 2026-09-17]
kicadlibs/models/Ublox_LEA_M8T.step
17.0 x 22.4 x 2.40 mm
Cut - PCB
Cut - Connectors
Body - Shield
