npgo22/APRL-Electrical/kicadlibs/models/LED_0603_1608Metric.step

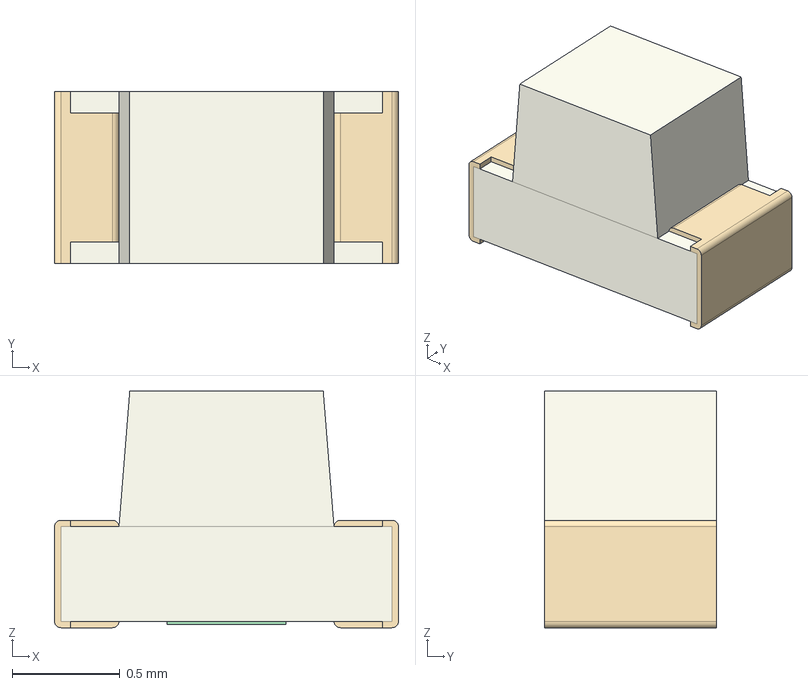
[picture p78: CAD file, 2026-09-17]
kicadlibs/models/LED_0603_1608Metric.step
1.60 x 0.8 x 1.10 mm
