npgo22/APRL-Electrical/kicadlibs/models/C_0603_1608Metric.step

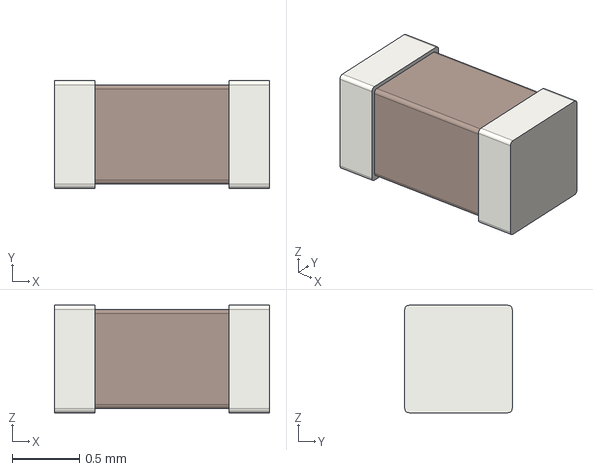
[picture p80: CAD file, 2026-09-17]
kicadlibs/models/C_0603_1608Metric.step
1.60 x 0.8 x 0.8 mm
