npgo22/APRL-Electrical/kicadlibs/models/QFN-68-1EP_8x8mm_P0.4mm_EP5.2x5.2mm.step

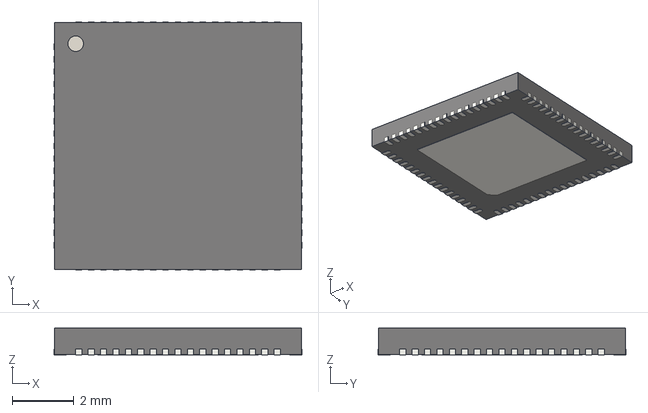
[picture p81: CAD file, 2026-09-17]
kicadlibs/models/QFN-68-1EP_8x8mm_P0.4mm_EP5.2x5.2mm.step
8.00 x 8.00 x 0.87 mm
