npgo22/APRL-Electrical/kicadlibs/models/SMA-TH_BWSMA-KWE-Z001.step

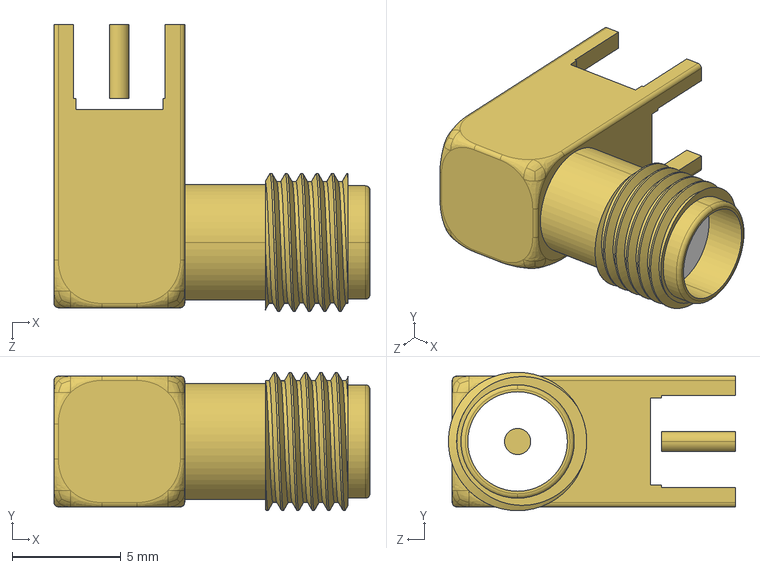
[picture p82: CAD file, 2026-09-17]
kicadlibs/models/SMA-TH_BWSMA-KWE-Z001.step
14.5 x 6.35 x 13.2 mm
