npgo22/APRL-Electrical/kicadlibs/models/PinHeader_1x07_P2.54mm_Vertical.step

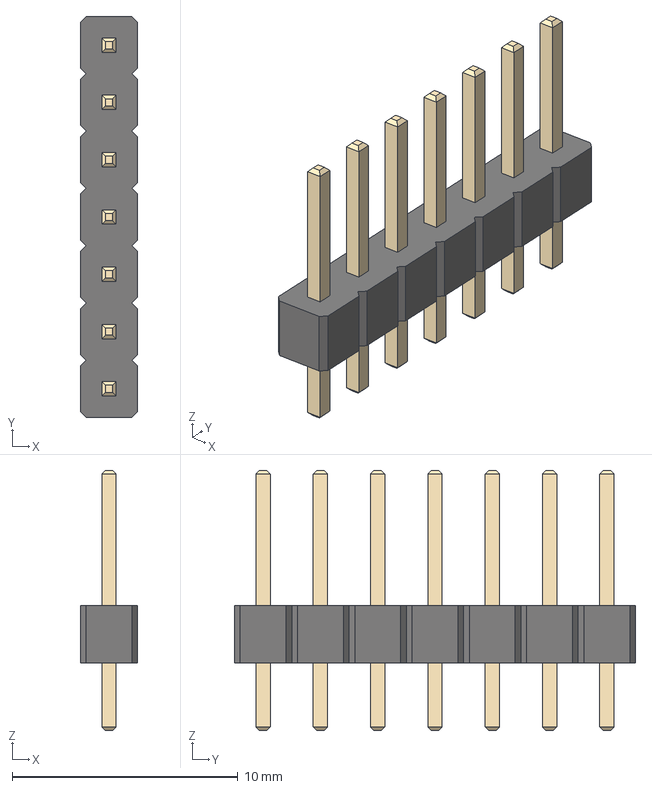
[picture p83: CAD file, 2026-09-17]
kicadlibs/models/PinHeader_1x07_P2.54mm_Vertical.step
2.54 x 17.8 x 11.5 mm
