npgo22/APRL-Electrical/kicadlibs/models/RJ45-TH_HY951180A.step

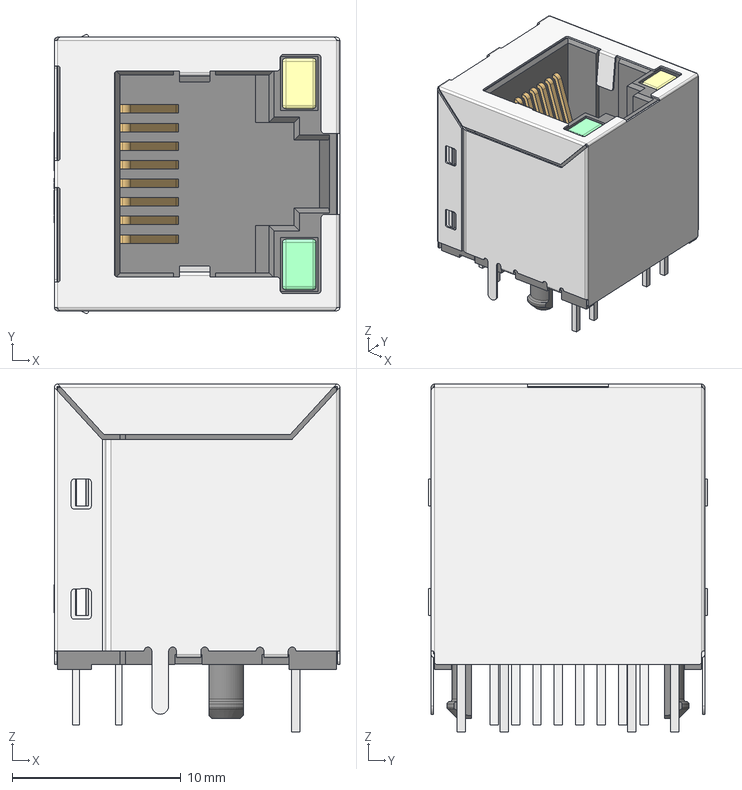
[picture p84: CAD file, 2026-09-17]
kicadlibs/models/RJ45-TH_HY951180A.step
16.9 x 16.5 x 20.6 mm
