npgo22/APRL-Electrical/kicadlibs/models/mps_dcdc_nxe2s_mc_a.step

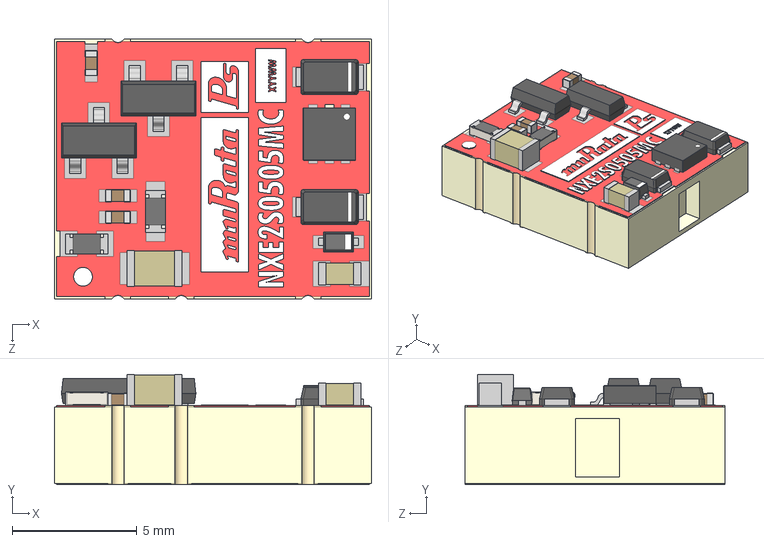
[picture p85: CAD file, 2026-09-17]
kicadlibs/models/mps_dcdc_nxe2s_mc_a.step
12.7 x 4.41 x 10.4 mm
