npgo22/APRL-Electrical/kicadlibs/models/PinHeader_2x05_P2.54mm_Vertical.step

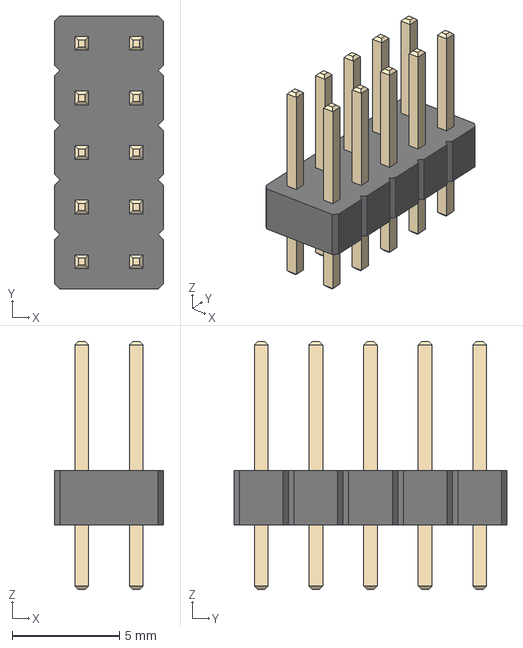
[picture p86: CAD file, 2026-09-17]
kicadlibs/models/PinHeader_2x05_P2.54mm_Vertical.step
5.08 x 12.7 x 11.5 mm
