npgo22/APRL-Electrical/kicadlibs/models/QFN-24_4x4mm_P0.5mm.step

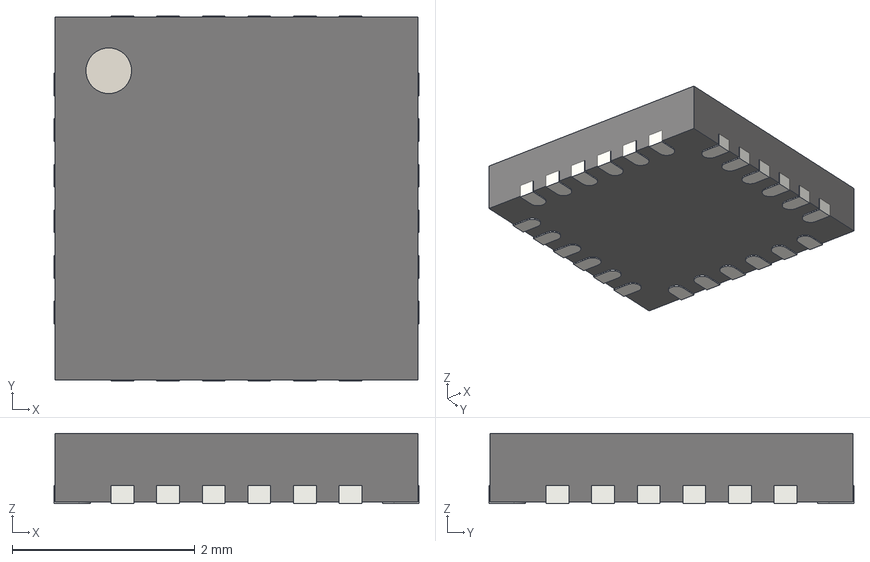
[picture p87: CAD file, 2026-09-17]
kicadlibs/models/QFN-24_4x4mm_P0.5mm.step
4.00 x 4.00 x 0.77 mm
