npgo22/APRL-Electrical/kicadlibs/models/SOT-23-6.step

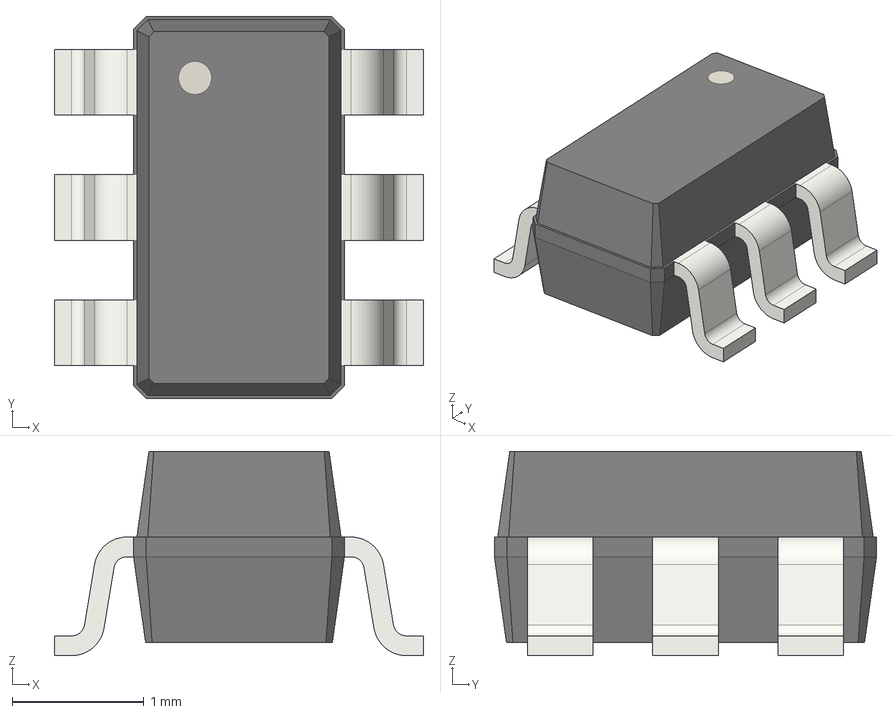
[picture p89: CAD file, 2026-09-17]
kicadlibs/models/SOT-23-6.step
2.80 x 2.90 x 1.55 mm
