npgo22/APRL-Electrical/kicadlibs/models/Crystal_SMD_3225-4Pin_3.2x2.5mm.step

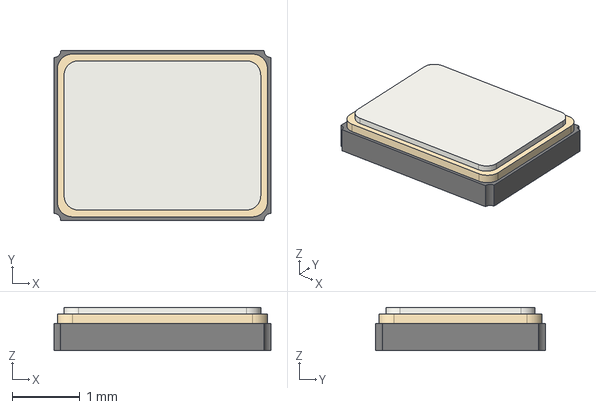
[picture p90: CAD file, 2026-09-17]
kicadlibs/models/Crystal_SMD_3225-4Pin_3.2x2.5mm.step
3.20 x 2.50 x 0.64 mm
