npgo22/APRL-Electrical/kicadlibs/models/SW-SMD_4P-L4.2-W3.2-P2.15-LS4.6-2.step

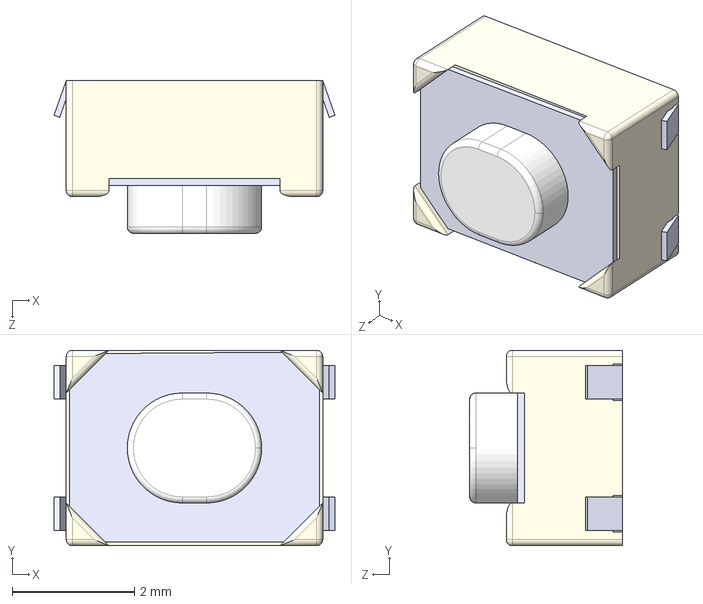
[picture p91: CAD file, 2026-09-17]
kicadlibs/models/SW-SMD_4P-L4.2-W3.2-P2.15-LS4.6-2.step
4.60 x 3.20 x 2.50 mm
