npgo22/APRL-Electrical/kicadlibs/models/Molex_CLIK-Mate_503175-0600_1x06-1MP_P1.50mm_Horizontal.step

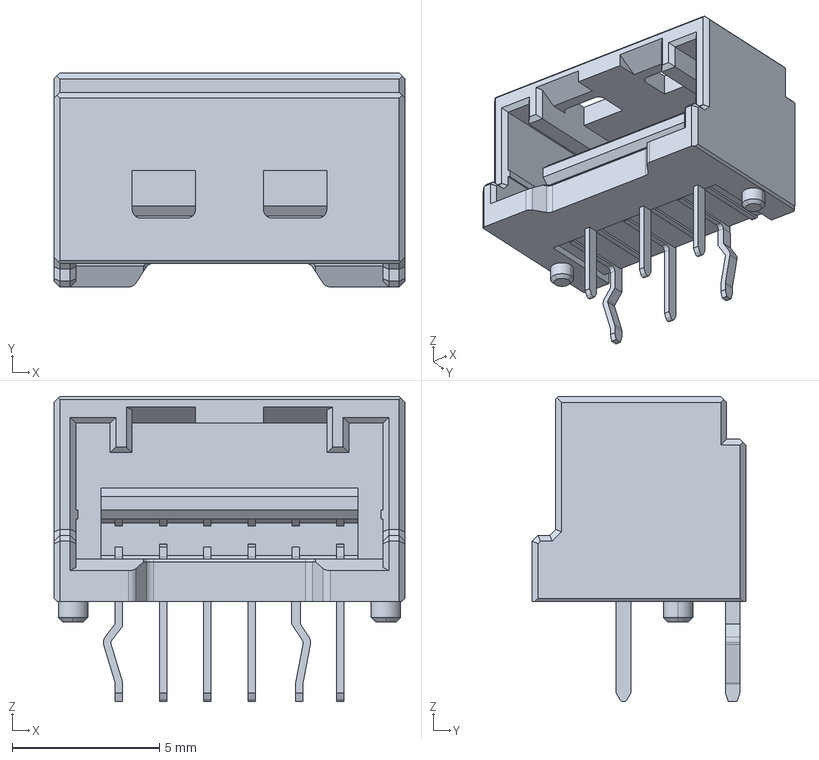
[picture p92: CAD file, 2026-09-17]
kicadlibs/models/Molex_CLIK-Mate_503175-0600_1x06-1MP_P1.50mm_Horizontal.step
11.9 x 7.25 x 10.4 mm
