npgo22/APRL-Electrical/kicadlibs/models/USB-C-SMD_GT-USB-7051A.step

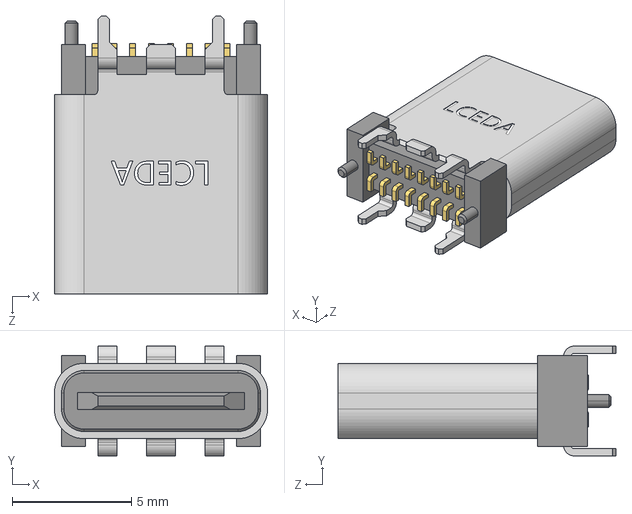
[picture p93: CAD file, 2026-09-17]
kicadlibs/models/USB-C-SMD_GT-USB-7051A.step
8.94 x 4.60 x 11.7 mm
