npgo22/APRL-Electrical/kicadlibs/models/TSSOP-14_4.4x5mm_P0.65mm.step

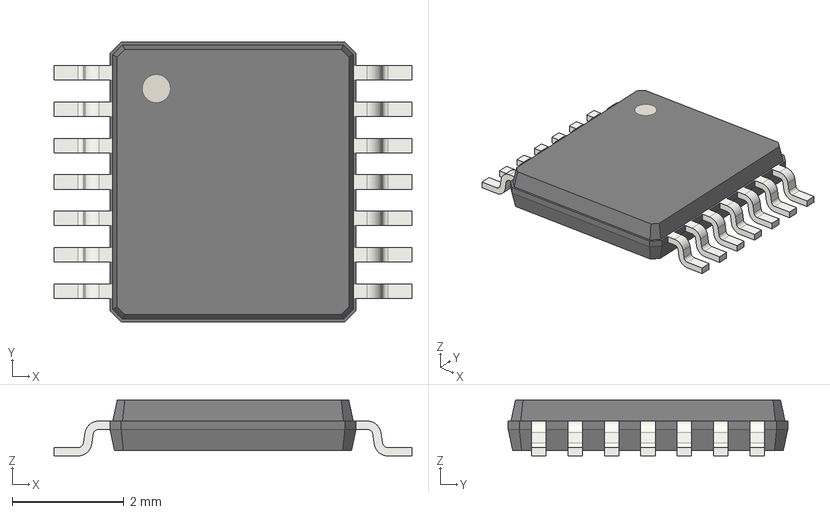
[picture p94: CAD file, 2026-09-17]
kicadlibs/models/TSSOP-14_4.4x5mm_P0.65mm.step
6.40 x 5.00 x 1.00 mm
