npgo22/APRL-Electrical/kicadlibs/models/Molex_CLIK-Mate_503159-0301_1x03-1MP_P1.50mm_Vertical.step

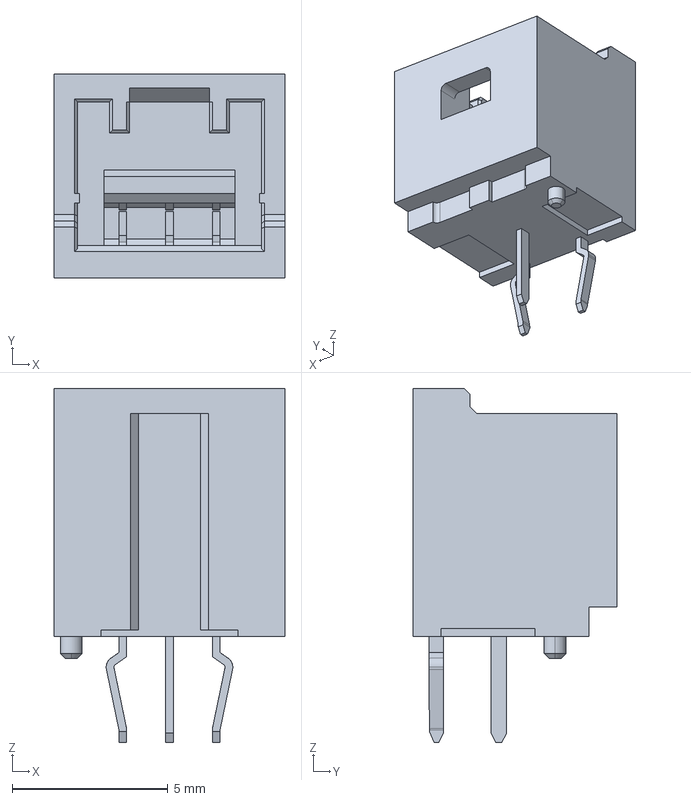
[picture p95: CAD file, 2026-09-17]
kicadlibs/models/Molex_CLIK-Mate_503159-0301_1x03-1MP_P1.50mm_Vertical.step
7.40 x 6.55 x 11.4 mm
