npgo22/APRL-Electrical/kicadlibs/models/D_SOD-123F.step

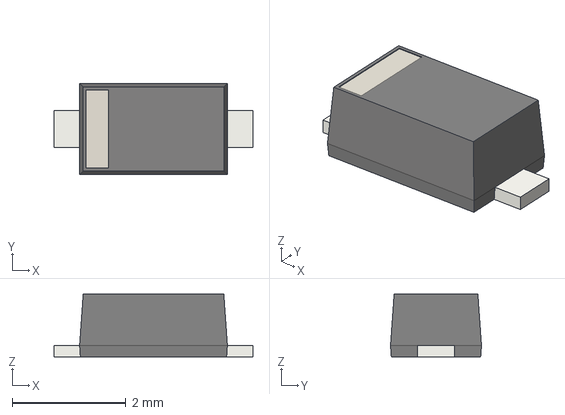
[picture p96: CAD file, 2026-09-17]
kicadlibs/models/D_SOD-123F.step
3.50 x 1.60 x 1.10 mm
