npgo22/APRL-Electrical/kicadlibs/models/ec11e18244au.step

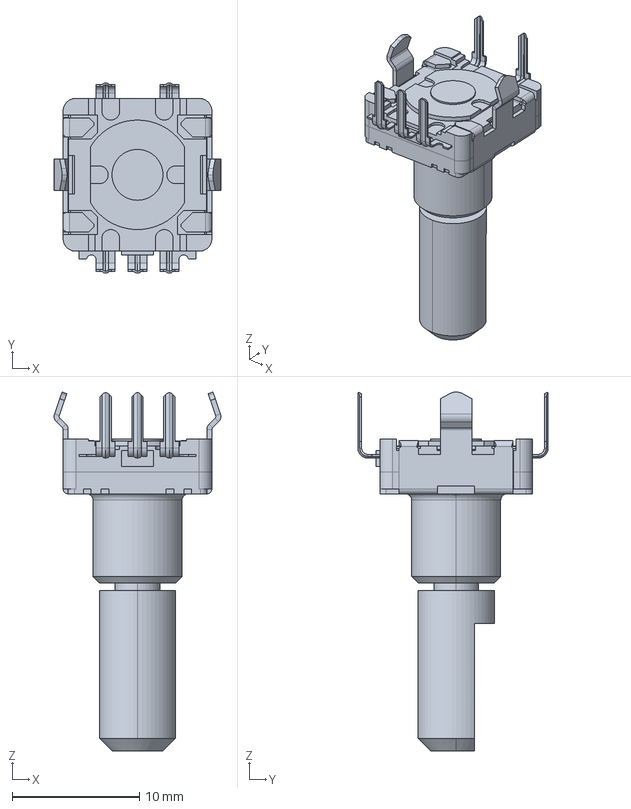
[picture p97: CAD file, 2026-09-17]
kicadlibs/models/ec11e18244au.step
13.1 x 15.0 x 28.2 mm
