npgo22/APRL-Electrical/kicadlibs/models/TSSOP-20_4.4x6.5mm_P0.65mm.step

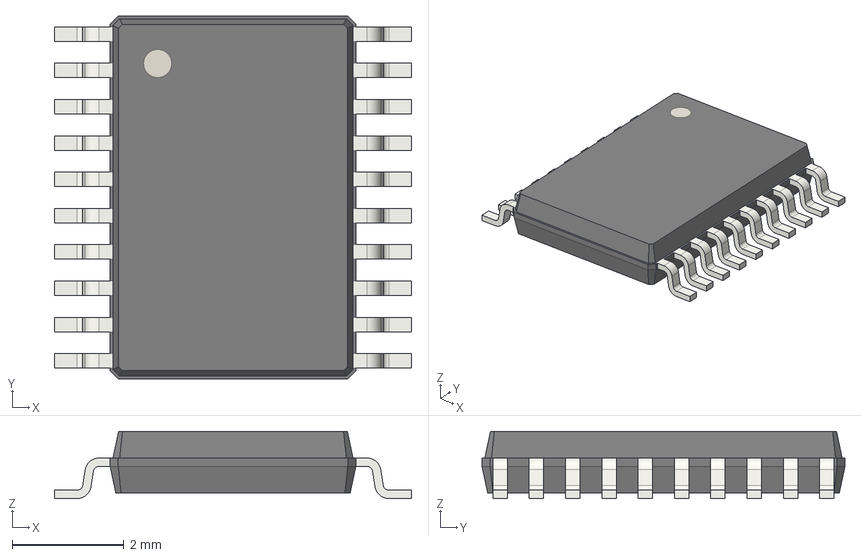
[picture p98: CAD file, 2026-09-17]
kicadlibs/models/TSSOP-20_4.4x6.5mm_P0.65mm.step
6.40 x 6.50 x 1.20 mm
