npgo22/APRL-Electrical/kicadlibs/models/Molex_CLIK-Mate_503159-0701_1x07-1MP_P1.50mm_Vertical.step

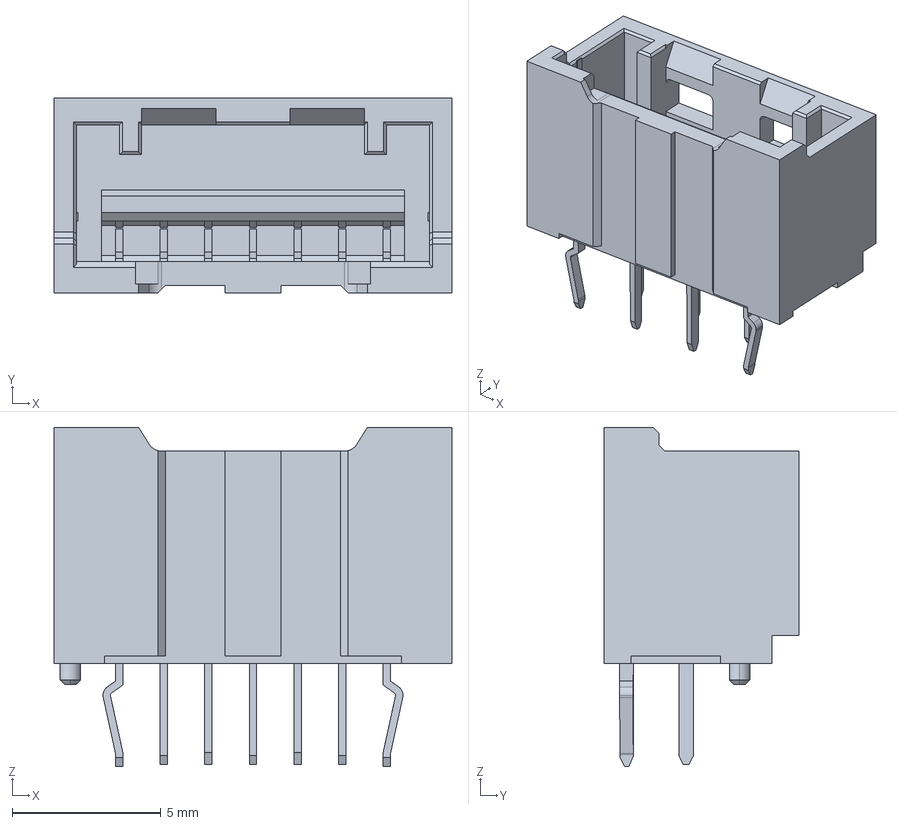
[picture p99: CAD file, 2026-09-17]
kicadlibs/models/Molex_CLIK-Mate_503159-0701_1x07-1MP_P1.50mm_Vertical.step
13.4 x 6.55 x 11.4 mm
