npgo22/APRL-Electrical/kicadlibs/models/Molex_CLIK-Mate_503175-0400_1x04-1MP_P1.50mm_Horizontal.step

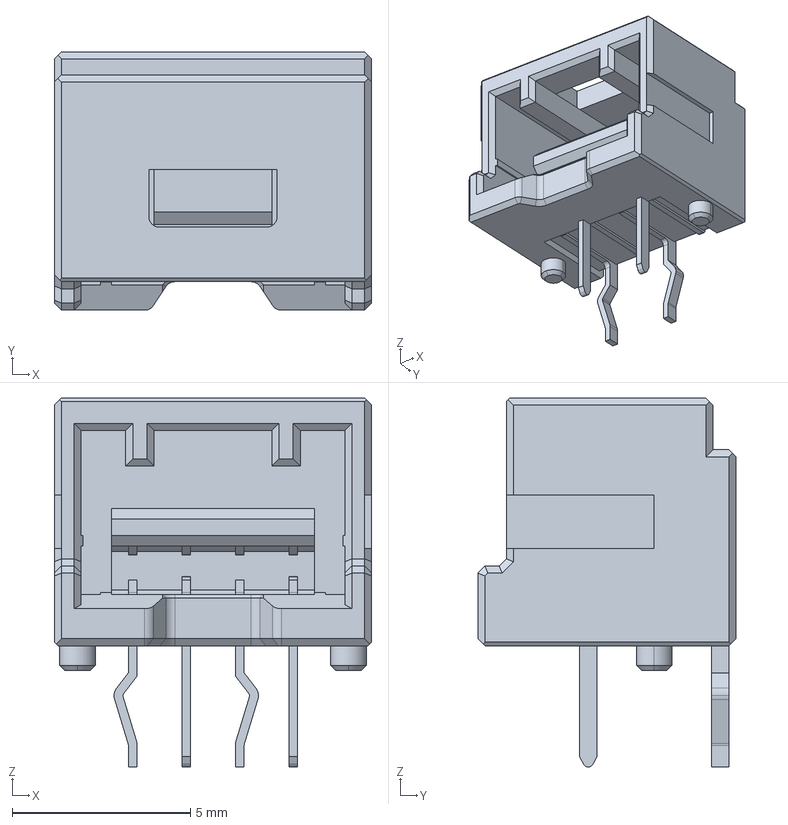
[picture p102: CAD file, 2026-09-17]
kicadlibs/models/Molex_CLIK-Mate_503175-0400_1x04-1MP_P1.50mm_Horizontal.step
8.90 x 7.25 x 10.4 mm
