npgo22/APRL-Electrical/kicadlibs/models/TerminalBlock_Phoenix_MPT-0,5-4-2.54_1x04_P2.54mm_Horizontal.step

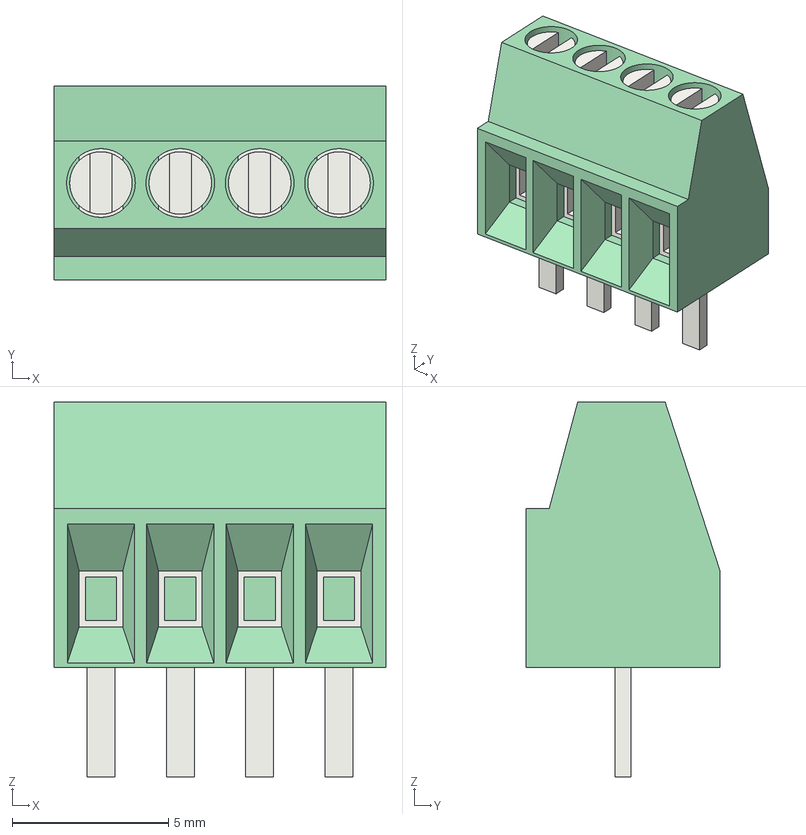
[picture p103: CAD file, 2026-09-17]
kicadlibs/models/TerminalBlock_Phoenix_MPT-0,5-4-2.54_1x04_P2.54mm_Horizontal.step
10.6 x 6.20 x 12.0 mm
