npgo22/APRL-Electrical/kicadlibs/models/DIP-4_W7.62mm_SMDSocket.step

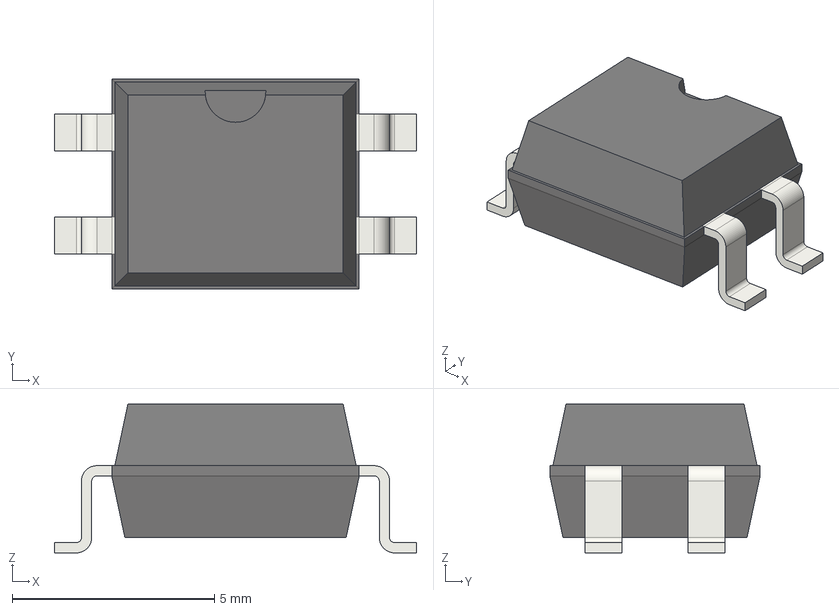
[picture p104: CAD file, 2026-09-17]
kicadlibs/models/DIP-4_W7.62mm_SMDSocket.step
8.95 x 5.20 x 3.68 mm
