npgo22/APRL-Electrical/kicadlibs/models/SOT-23.step

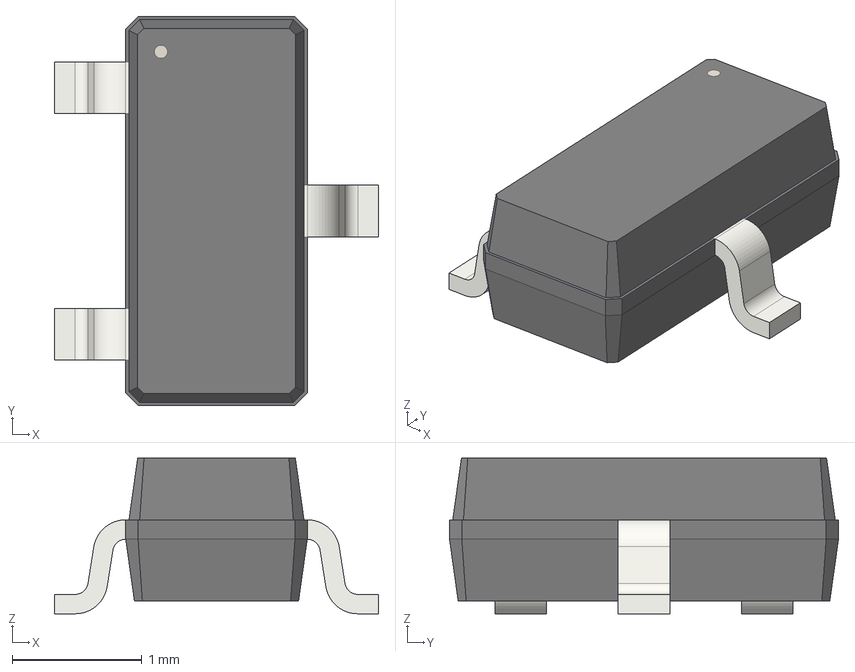
[picture p106: CAD file, 2026-09-17]
kicadlibs/models/SOT-23.step
2.50 x 3.00 x 1.20 mm
