npgo22/APRL-Electrical/kicadlibs/models/s0981-46r.step

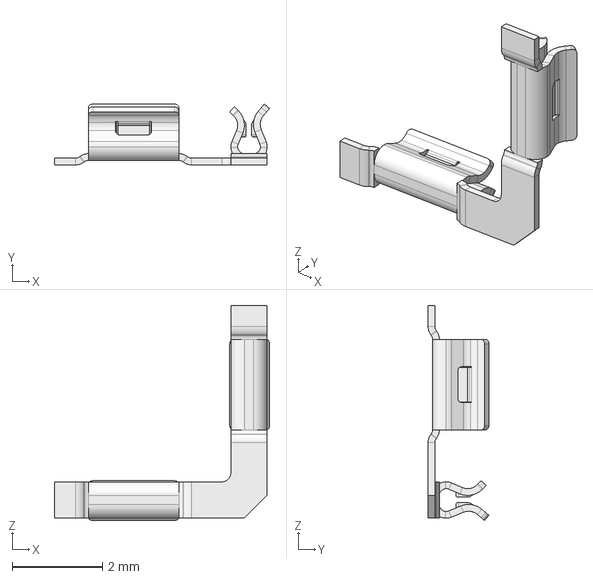
[picture p107: CAD file, 2026-09-17]
kicadlibs/models/s0981-46r.step
4.75 x 1.35 x 4.75 mm
