npgo22/APRL-Electrical/kicadlibs/models/TerminalBlock_Phoenix_MPT-0,5-5-2.54_1x05_P2.54mm_Horizontal.step

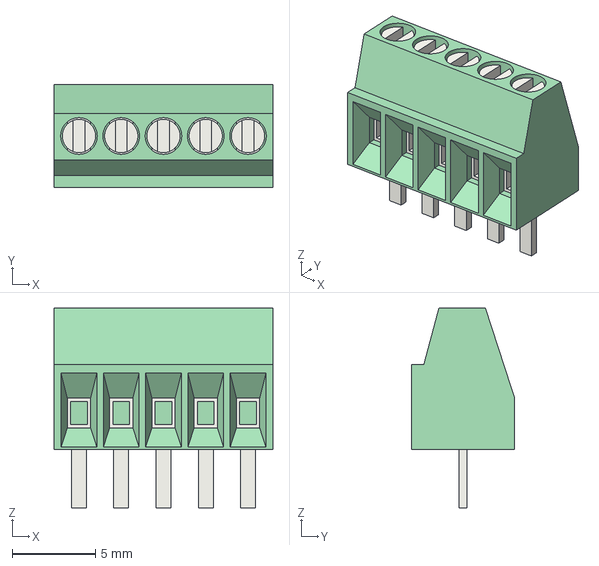
[picture p108: CAD file, 2026-09-17]
kicadlibs/models/TerminalBlock_Phoenix_MPT-0,5-5-2.54_1x05_P2.54mm_Horizontal.step
13.2 x 6.20 x 12.0 mm
