npgo22/APRL-Electrical/kicadlibs/models/TerminalBlock_Phoenix_MPT-0,5-2-2.54_1x02_P2.54mm_Horizontal.step

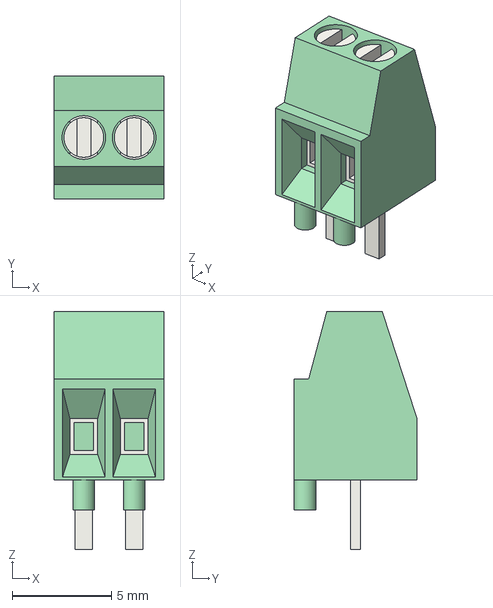
[picture p110: CAD file, 2026-09-17]
kicadlibs/models/TerminalBlock_Phoenix_MPT-0,5-2-2.54_1x02_P2.54mm_Horizontal.step
5.54 x 6.20 x 12.0 mm
